shmoergh/hog-moduleur/05-adsr-vca/electronics/core/adsr-vca-core.kicad_pcb

## KiCad design 05-adsr-vca/electronics/core/adsr-vca-core.kicad_pcb (2025-10-25)

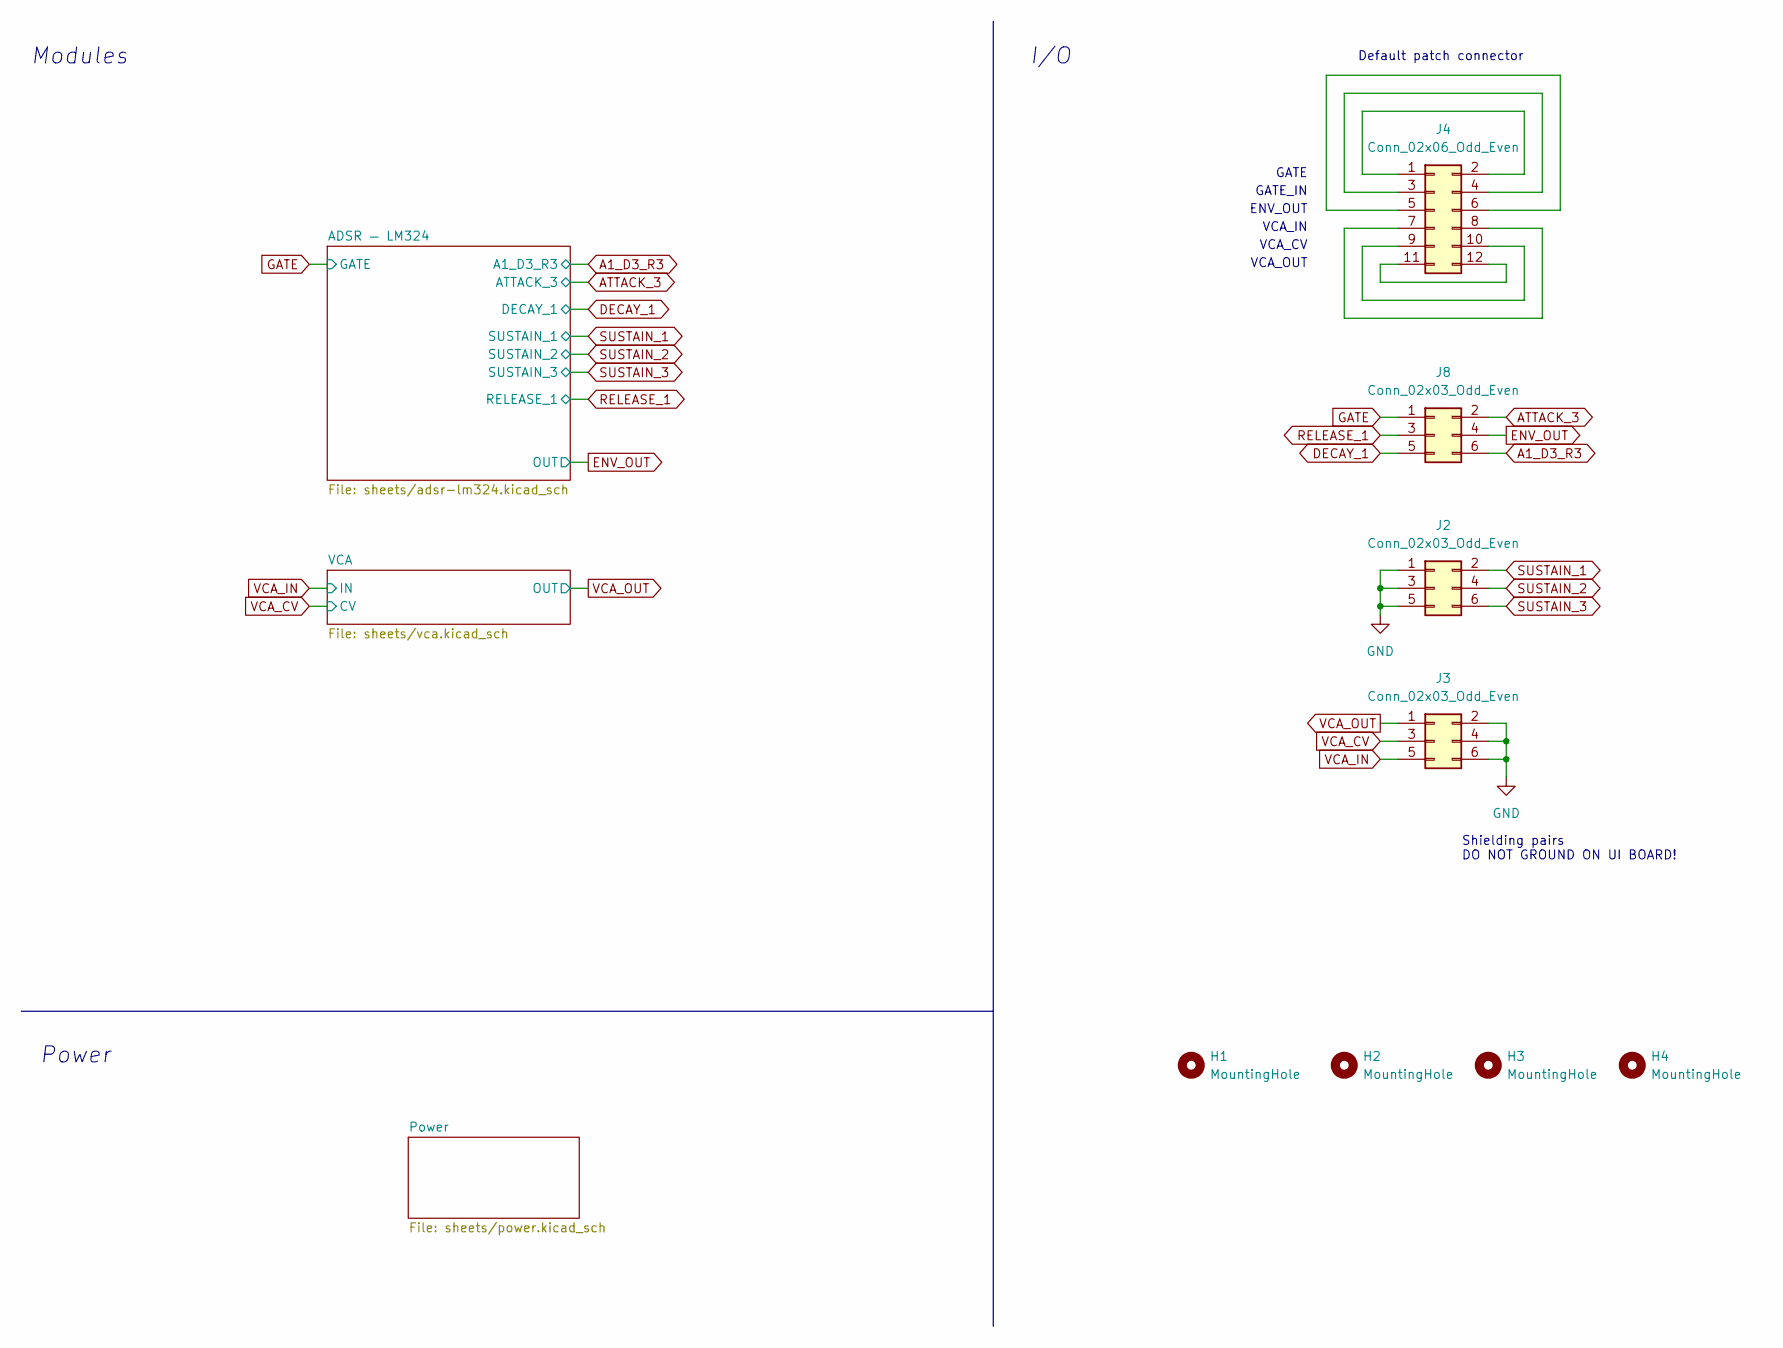
[picture p48: schematic adsr-vca-core.kicad_sch]

Parts:
H1, H2, H3, H4: MountingHole; MountingHole_3.2mm_M3_DIN965_Pad
J2, J3, J8: Conn_02x03_Odd_Even; PinHeader_2x03_P2.54mm_Vertical
J4: Conn_02x06_Odd_Even; PinHeader_2x06_P2.54mm_Vertical

Connections:
A1_D3_R3: J8.6; also elsewhere on the board
ATTACK_3: J8.2; also elsewhere on the board
DECAY_1: J8.5; also elsewhere on the board
ENV_OUT: J8.4; also elsewhere on the board
GATE: J8.1; also elsewhere on the board
GND: J2.1, J2.3, J2.5, J3.2, J3.4, J3.6; also elsewhere on the board
unnamed: J4.1, J4.2
unnamed: J4.3, J4.4
unnamed: J4.5, J4.6
unnamed: J4.7, J4.8
unnamed: J4.9, J4.10
unnamed: J4.11, J4.12
RELEASE_1: J8.3; also elsewhere on the board
SUSTAIN_1: J2.2; also elsewhere on the board
SUSTAIN_2: J2.4; also elsewhere on the board
SUSTAIN_3: J2.6; also elsewhere on the board
VCA_CV: J3.3; also elsewhere on the board
VCA_IN: J3.5; also elsewhere on the board
VCA_OUT: J3.1; also elsewhere on the board

Notes on the sheet:
Power
ENV_OUT
Default patch connector
VCA_OUT
GATE
Shielding pairs DO NOT GROUND ON UI BOARD!
VCA_CV
Modules
GATE_IN
I/O
VCA_IN

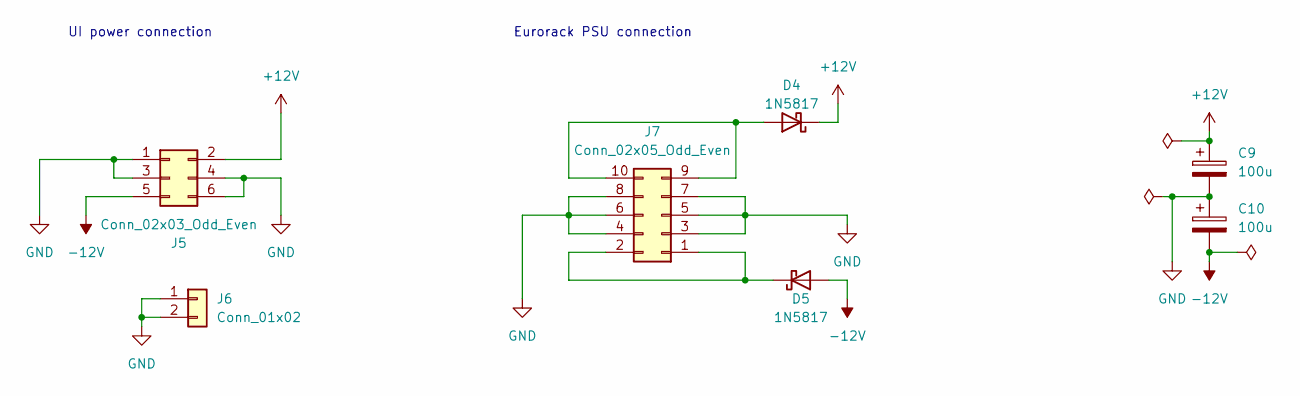
[picture p49: schematic power.kicad_sch]

Parts:
C9, C10: 100u; CP_Elec_6.3x7.7; LCSC C2836437
D4, D5: 1N5817; D_SOD-323; LCSC C5190152
J5: Conn_02x03_Odd_Even; PinHeader_2x03_P2.54mm_Vertical
J6: Conn_01x02; PinHeader_1x02_P2.54mm_Vertical
J7: Conn_02x05_Odd_Even; IDC-Header_2x05_P2.54mm_Horizontal

Connections:
+12V: C9.1, D4.1 (K), J5.2; also elsewhere on the board
-12V: C10.2, D5.2 (A), J5.5; also elsewhere on the board
GND: C9.2, C10.1, J5.1, J5.3, J5.4, J5.6, J6.1, J6.2, J7.3, J7.4, J7.5, J7.6, J7.7, J7.8; also elsewhere on the board
unnamed: D4.2 (A), J7.9, J7.10
unnamed: D5.1 (K), J7.1, J7.2

Notes on the sheet:
UI power connection
Eurorack PSU connection

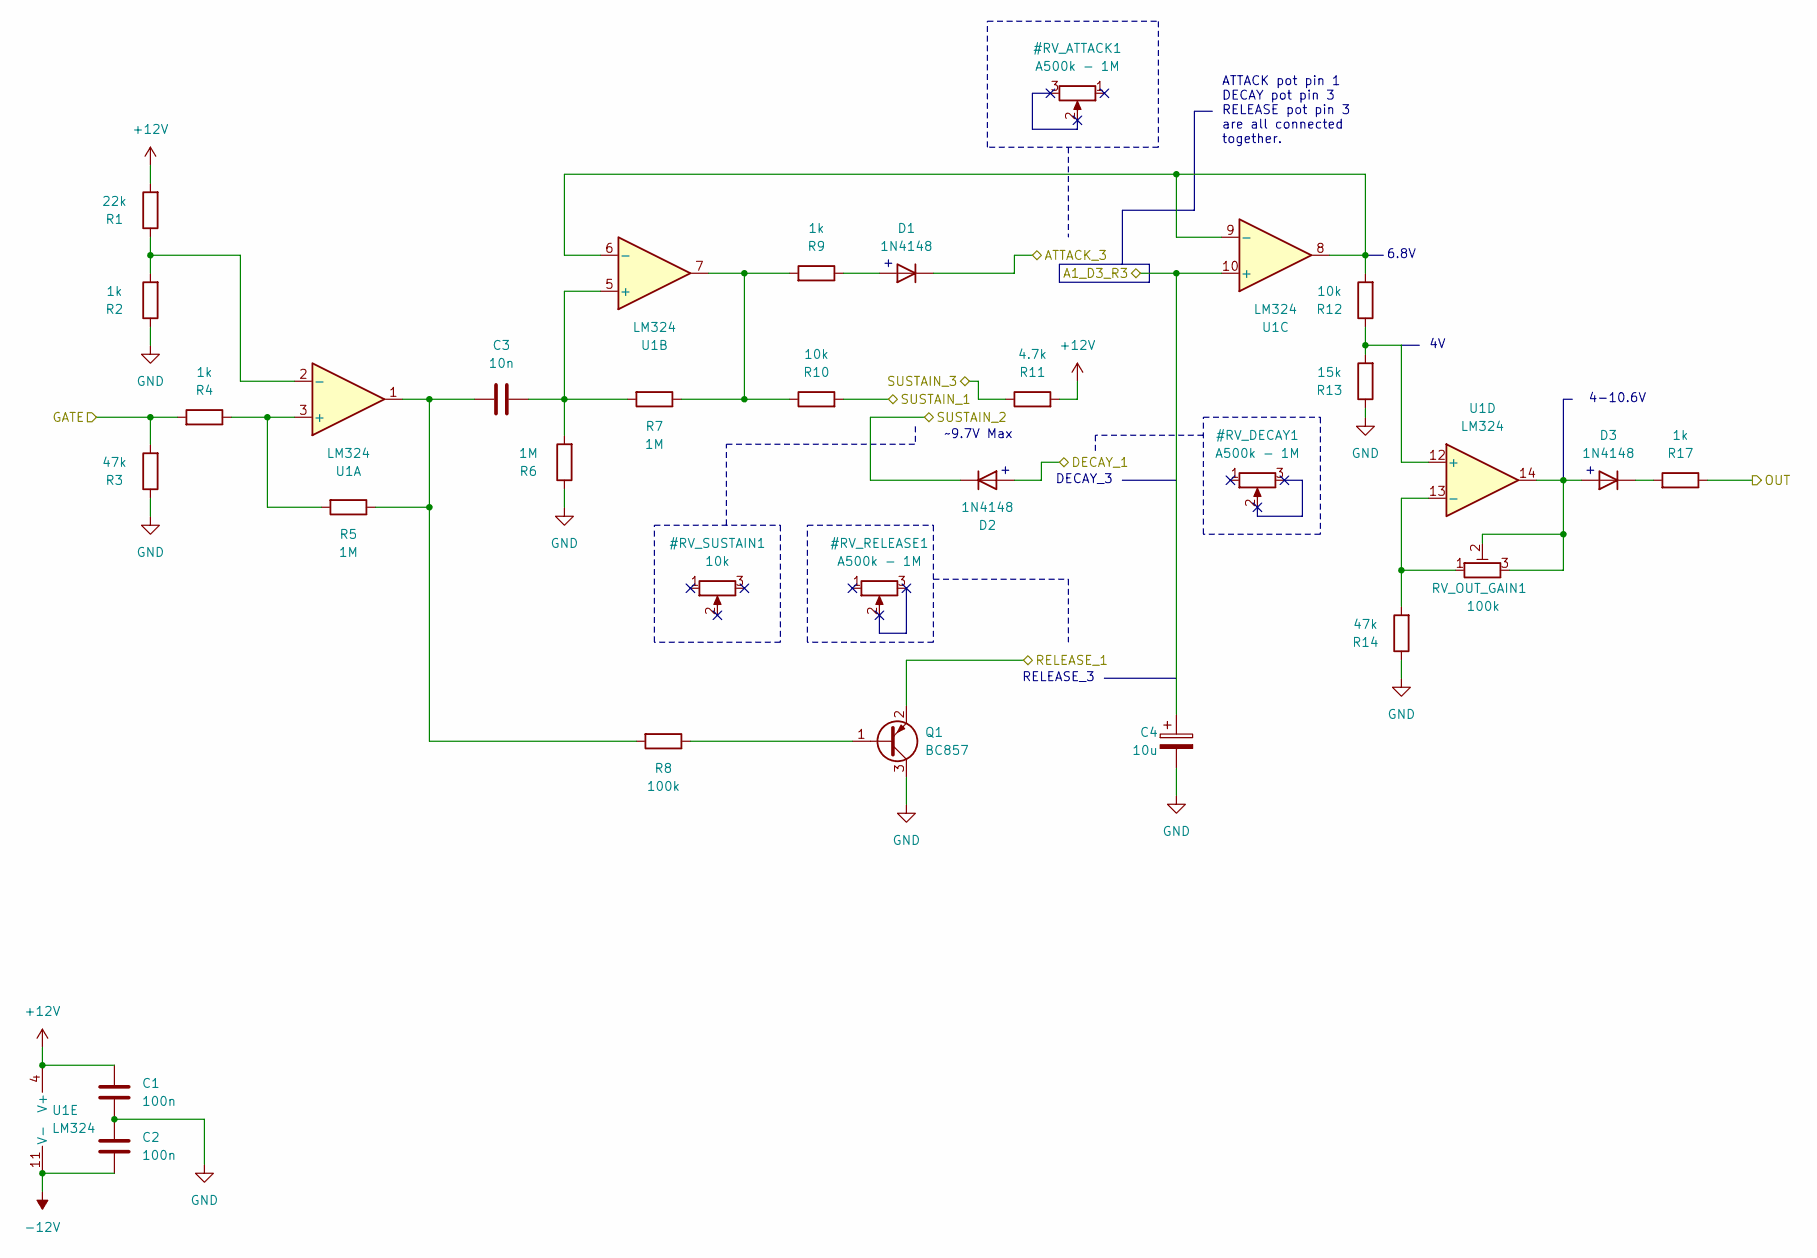
[picture p50: schematic adsr-lm324.kicad_sch, Hog Moduelur — ADSR]

Parts:
C1, C2: 100n; C_0603_1608Metric; LCSC C14663
C3: 10n; C_0603_1608Metric; LCSC C57112
C4: 10u; CP_Elec_5x5.4; LCSC C30110
D1, D2, D3: 1N4148; D_SOD-123; LCSC C81598
Q1: BC857; SOT-23; LCSC C20069137
R1: 22k; R_0603_1608Metric; LCSC C31850
R2, R4, R9, R17: 1k; R_0603_1608Metric; LCSC C21190
R3, R14: 47k; R_0603_1608Metric; LCSC C25819
R5, R6, R7: 1M; R_0603_1608Metric; LCSC C22935
R8: 100k; R_0603_1608Metric; LCSC C25803
R10, R12: 10k; R_0603_1608Metric; LCSC C25804
R11: 4.7k; R_0603_1608Metric; LCSC C23162
R13: 15k; R_0603_1608Metric; LCSC C22809
RV_OUT_GAIN1: 100k; Potentiometer_ACP_CA6-H2,5_Horizontal
U1: LM324; SOIC-14_3.9x8.7mm_P1.27mm; LCSC C71035

Connections:
+12V: C1.1, R1.2, R11.2, U1.4 (V+); also elsewhere on the board
-12V: C2.2, U1.11 (V-); also elsewhere on the board
A1_D3_R3: C4.1, U1.10 (+); also elsewhere on the board
ATTACK_3: D1.1 (K); also elsewhere on the board
DECAY_1: D2.2 (A); also elsewhere on the board
ENV_OUT: R17.1; also elsewhere on the board
GATE: R3.2, R4.2; also elsewhere on the board
GND: C1.2, C2.1, C4.2, Q1.3 (C), R2.1, R3.1, R6.1, R13.1, R14.1; also elsewhere on the board
unnamed: C3.1, R5.1, R8.2, U1.1
unnamed: D1.2 (A), R9.1
unnamed: D3.2 (A), RV_OUT_GAIN1.2, RV_OUT_GAIN1.3, U1.14
unnamed: D3.1 (K), R17.2
unnamed: Q1.1 (B), R8.1
unnamed: R7.1, R9.2, R10.1, U1.7
unnamed: R4.1, R5.2, U1.3 (+)
unnamed: R1.1, R2.2, U1.2 (-)
unnamed: C3.2, R6.2, R7.2, U1.5 (+)
unnamed: R12.2, U1.6 (-), U1.8, U1.9 (-)
unnamed: R12.1, R13.2, U1.12 (+)
unnamed: R14.2, RV_OUT_GAIN1.1, U1.13 (-)
RELEASE_1: Q1.2 (E); also elsewhere on the board
SUSTAIN_1: R10.2; also elsewhere on the board
SUSTAIN_2: D2.1 (K); also elsewhere on the board
SUSTAIN_3: R11.1; also elsewhere on the board

Notes on the sheet:
4-10.6V
DECAY_3
~9.7V Max
RELEASE_3
6.8V
ATTACK pot pin 1 DECAY pot pin 3 RELEASE pot pin 3 are all connected together.

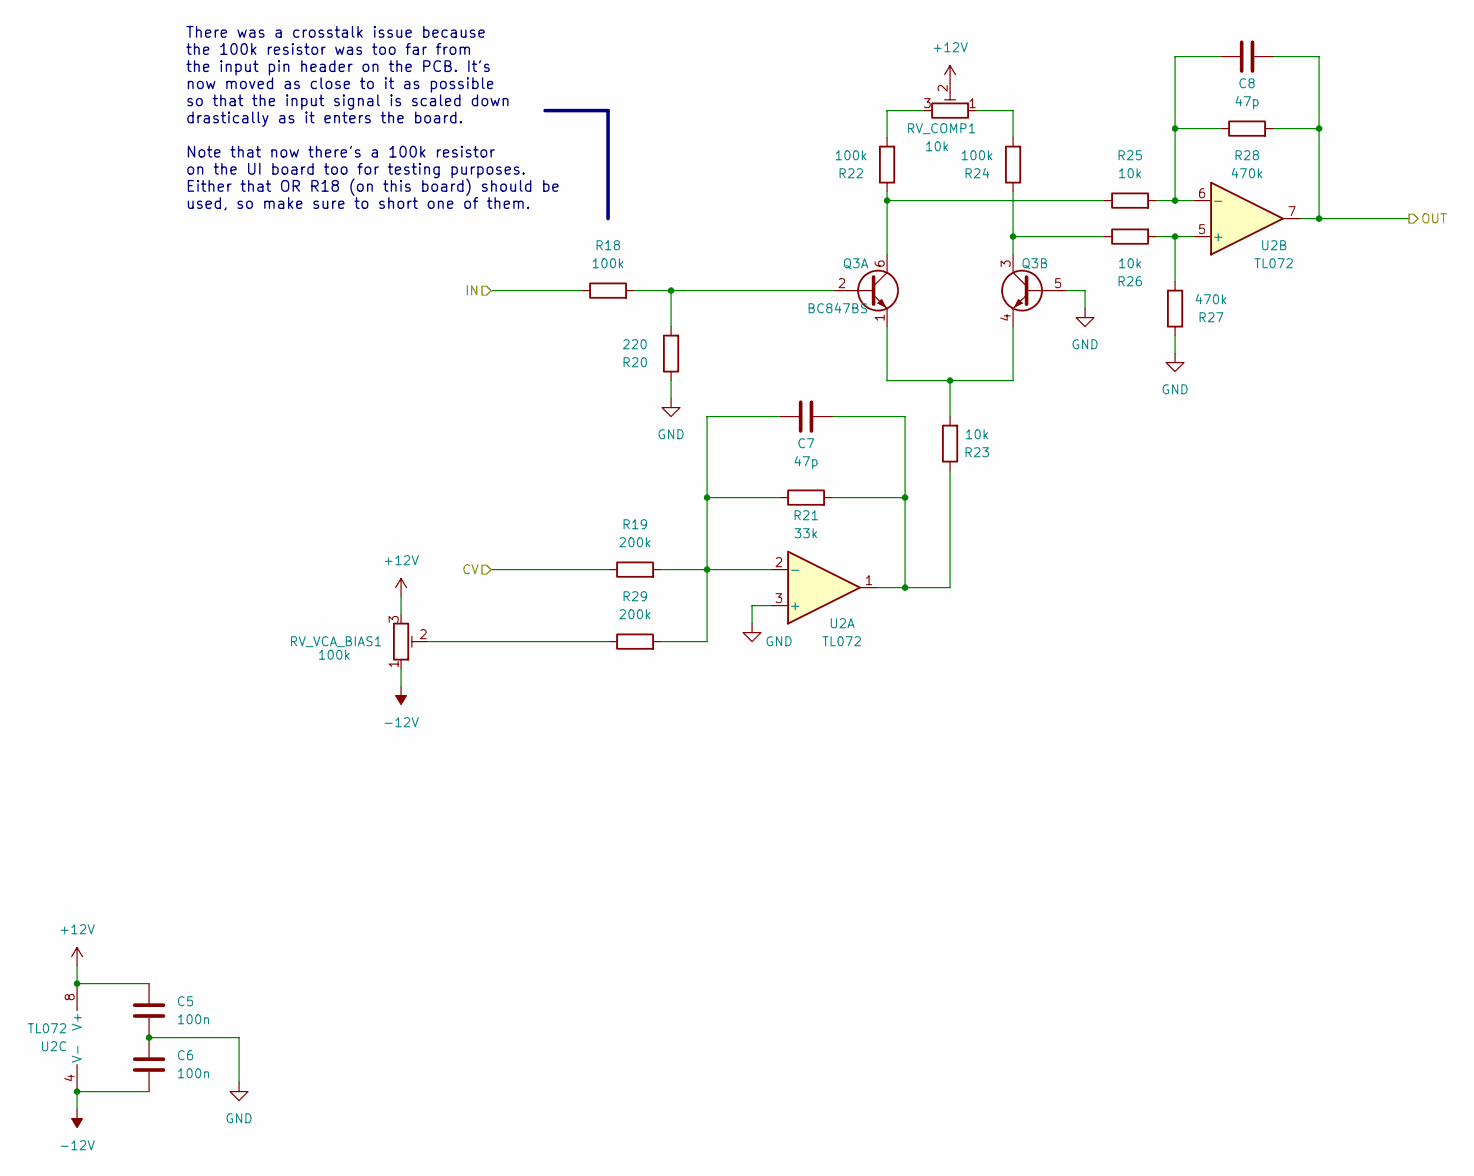
[picture p51: schematic vca.kicad_sch]

Parts:
C5, C6: 100n; C_0603_1608Metric; LCSC C14663
C7, C8: 47p; C_0603_1608Metric_Pad1.08x0.95mm_HandSolder; LCSC C1671
Q3: BC847BS; SOT-363_SC-70-6; LCSC C5380687
R18, R22, R24: 100k; R_0603_1608Metric; LCSC C25803
R19, R29: 200k; R_0603_1608Metric; LCSC C25811
R20: 220; R_0603_1608Metric; LCSC C22962
R21: 33k; R_0603_1608Metric; LCSC C4216
R23, R25, R26: 10k; R_0603_1608Metric; LCSC C25804
R27, R28: 470k; R_0603_1608Metric; LCSC C23178
RV_COMP1: 10k; Potentiometer_ACP_CA6-H2,5_Horizontal
RV_VCA_BIAS1: 100k; Potentiometer_ACP_CA6-H2,5_Horizontal
U2: TL072; SOIC-8_3.9x4.9mm_P1.27mm; LCSC C6961

Connections:
+12V: C5.1, RV_COMP1.2, RV_VCA_BIAS1.3, U2.8 (V+); also elsewhere on the board
-12V: C6.2, RV_VCA_BIAS1.1, U2.4 (V-); also elsewhere on the board
GND: C5.2, C6.1, Q3.5 (B2), R20.1, R27.1, U2.3 (+); also elsewhere on the board
unnamed: C7.2, R21.2, R23.1, U2.1
unnamed: Q3.2 (B1), R18.2, R20.2
unnamed: Q3.6 (C1), R22.1, R25.1
unnamed: Q3.1 (E1), Q3.4 (E2), R23.2
unnamed: Q3.3 (C2), R24.1, R26.1
unnamed: R22.2, RV_COMP1.3
unnamed: R24.2, RV_COMP1.1
unnamed: R29.1, RV_VCA_BIAS1.2
unnamed: C7.1, R19.2, R21.1, R29.2, U2.2 (-)
unnamed: R26.2, R27.2, U2.5 (+)
unnamed: C8.1, R25.2, R28.1, U2.6 (-)
VCA_CV: R19.1; also elsewhere on the board
VCA_IN: R18.1; also elsewhere on the board
VCA_OUT: C8.2, R28.2, U2.7; also elsewhere on the board

Notes on the sheet:
There was a crosstalk issue because the 100k resistor was too far from the input pin header on the PCB. It's now moved as close to it as possible so that the input signal is scaled down drastically as it enters the board. Note that now there's a 100k resistor on the UI board too for testing purpose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

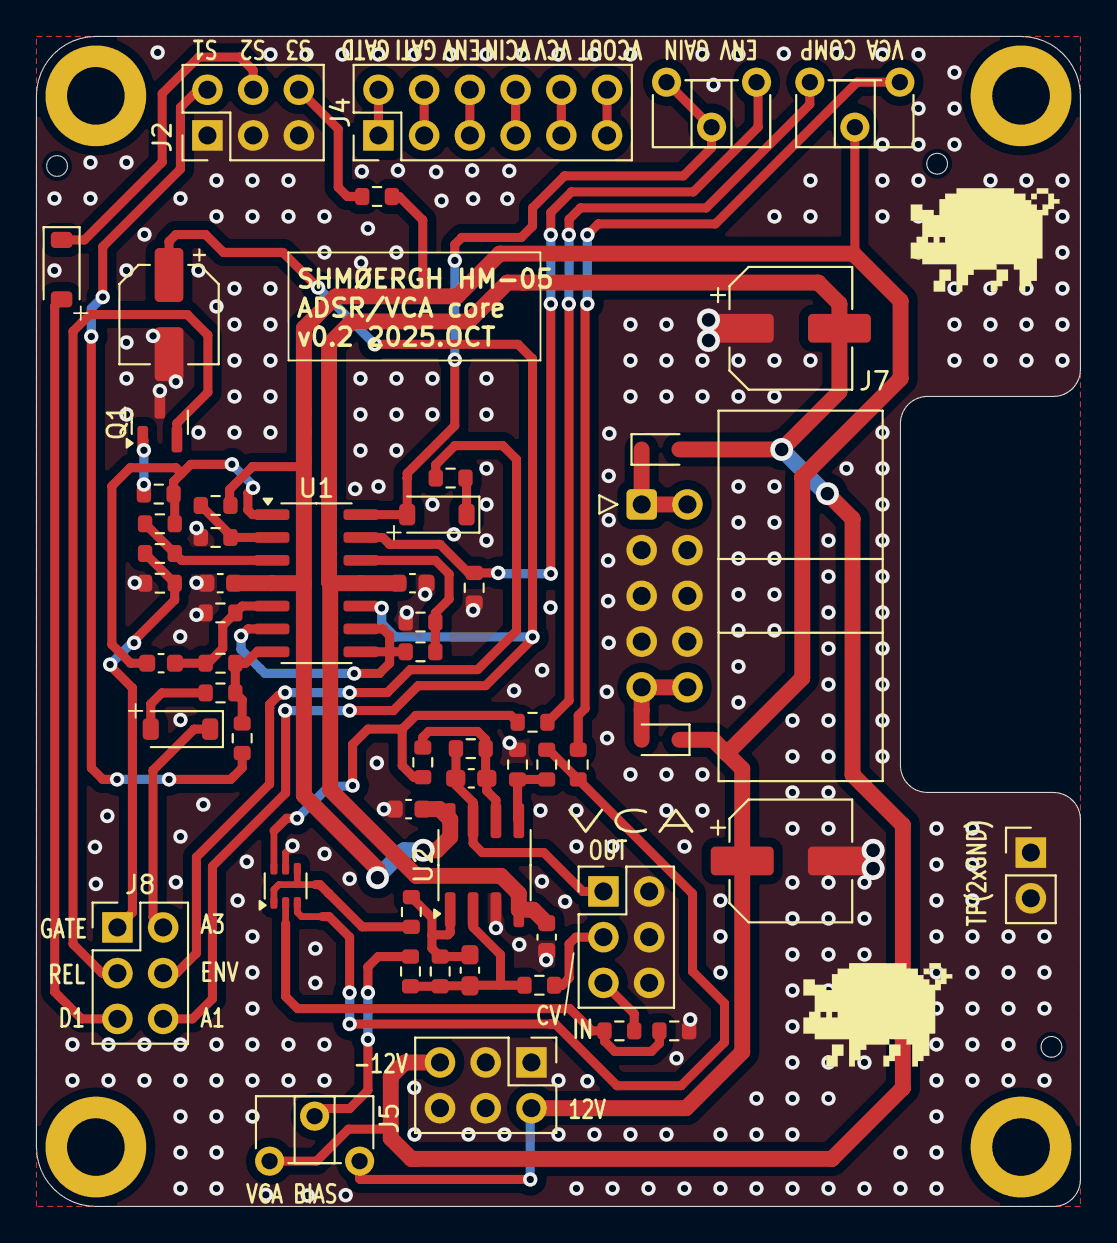
[picture p52: board adsr-vca-core.kicad_pcb from above]

Board: 2 copper layers, 58.0 x 65.0 mm, 60 parts (0 on the bottom side), 46 nets.
