shmoergh/hog-moduleur/04-vcf/electronics/core/vcf-core.kicad_pcb

## KiCad design 04-vcf/electronics/core/vcf-core.kicad_pcb (2025-10-25)

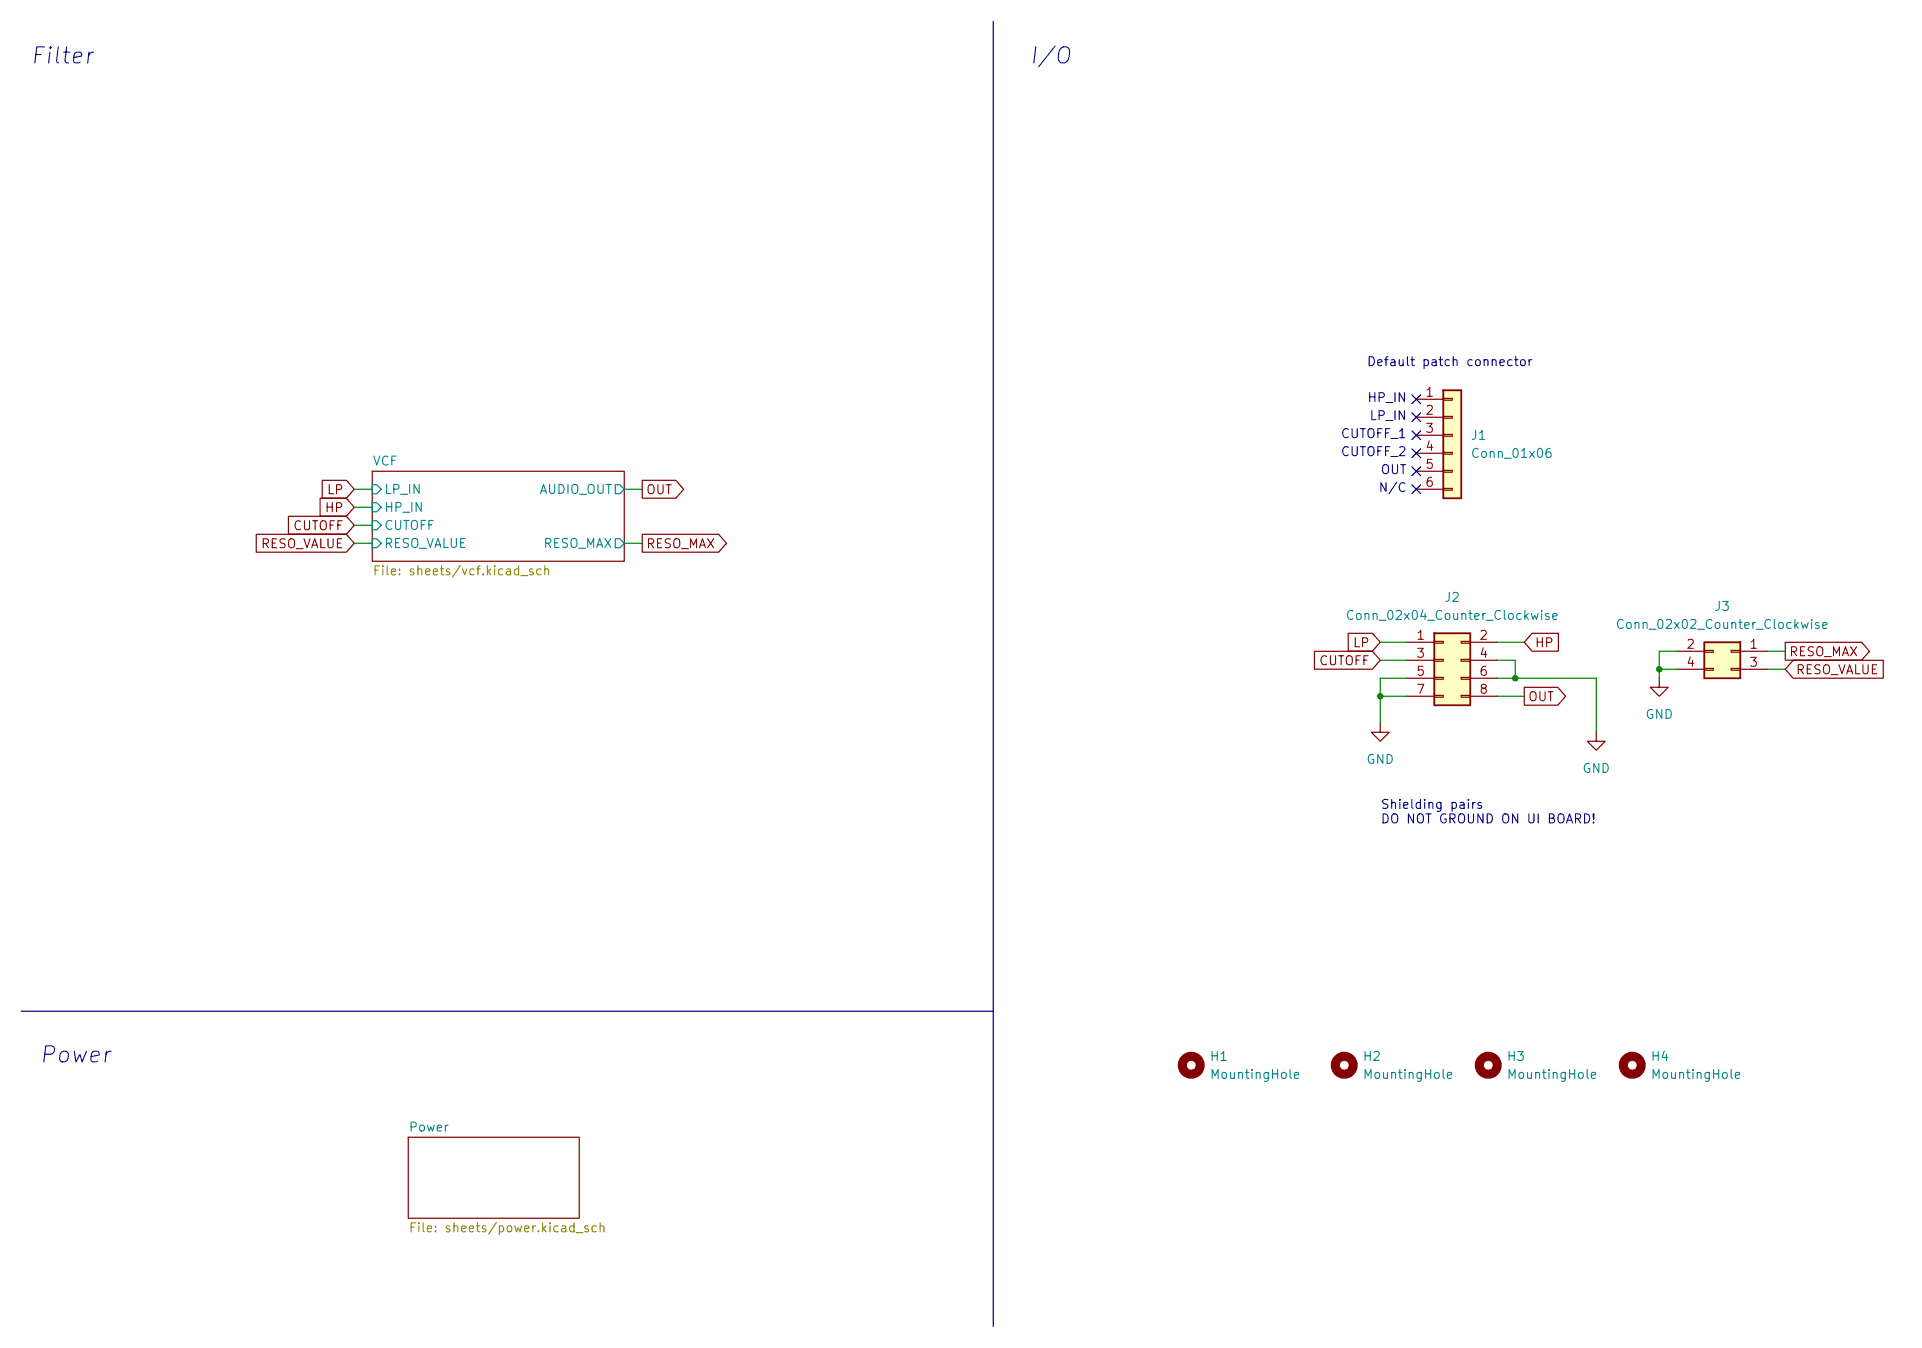
[picture p53: schematic vcf-core.kicad_sch, Hog Moduleur VCF]

Parts:
H1, H2, H3, H4: MountingHole; MountingHole_3.2mm_M3_DIN965_Pad
J1: Conn_01x06; PinHeader_1x06_P2.54mm_Vertical; Part no. 474-PRT-09280
J2: Conn_02x04_Counter_Clockwise; PinHeader_2x04_P2.54mm_Vertical; Part no. 200-HTSW10407TD
J3: Conn_02x02_Counter_Clockwise; PinHeader_2x02_P2.54mm_Vertical; Part no. 200-HTSW10207TD

Connections:
HP: J2.2; also elsewhere on the board
LP: J2.1; also elsewhere on the board
OUT: J2.8; also elsewhere on the board

Notes on the sheet:
Power
CUTOFF_1
Default patch connector
N/C
HP_IN
Shielding pairs DO NOT GROUND ON UI BOARD!
OUT
Filter
LP_IN
I/O
CUTOFF_2
