shmoergh/hog-moduleur/04-vcf/electronics/core/vcf-core.kicad_pcb

## KiCad design 04-vcf/electronics/core/vcf-core.kicad_pcb (continued)

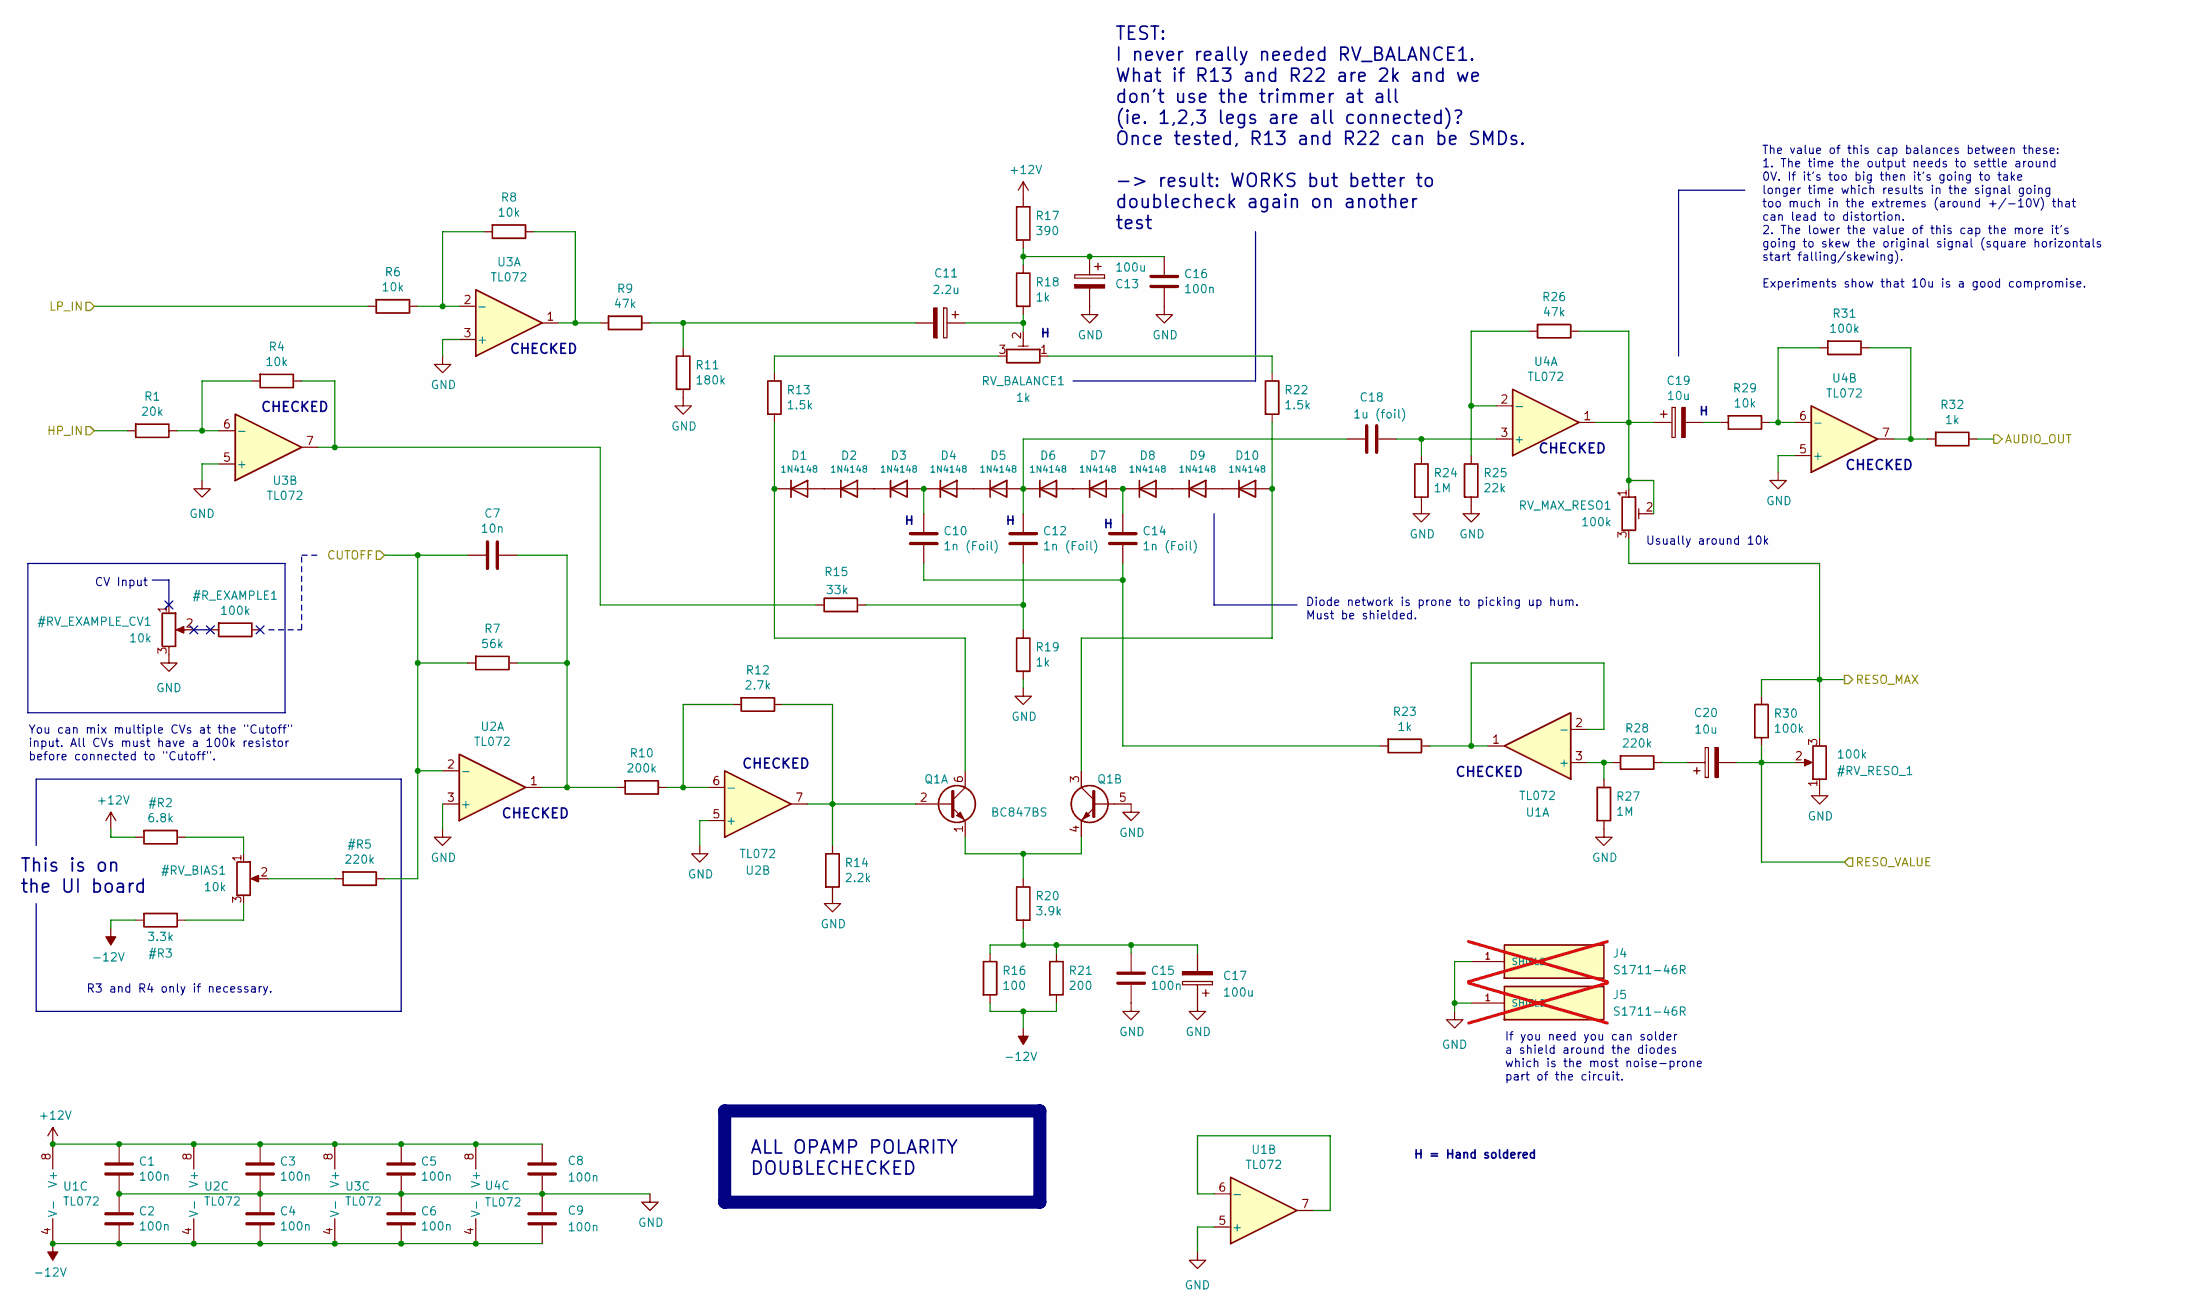
[picture p54: schematic vcf.kicad_sch]

Parts:
C1, C2, C3, C4, C5, C6, C8, C9, C15, C16: 100n; C_0603_1608Metric; LCSC C14663
C7: 10n; C_0603_1608Metric; LCSC C57112
C10, C12, C14: 1n (Foil); C_Rect_L7.0mm_W2.5mm_P5.00mm; Part no. 80-R82EC1100SH50J
C11: 2.2u; CP_Elec_4x5.7; LCSC C249889
C13, C17: 100u; CP_Elec_6.3x7.7; LCSC C2836437
C18: 1u (foil); C_Rect_L7.0mm_W4.5mm_P5.00mm; Part no. 80-R82EC1470DQ50K
C19: 10u; CP_Radial_D8.0mm_P5.00mm; Part no. 667-EEA-GA1V470B
C20: 10u; CP_Elec_4x5.4; LCSC C3343
D1, D2, D3, D4, D5, D6, D7, D8, D9, D10: 1N4148; D_SOD-123; LCSC C81598
J4, J5: S1711-46R; HARWIN_S1711-46R; PARTREV 23/10/18; not fitted
Q1: BC847BS; SOT-363_SC-70-6; LCSC C5380687
R1: 20k; R_0603_1608Metric_Pad0.98x0.95mm_HandSolder; LCSC C4184
R4, R6, R8, R29: 10k; R_0603_1608Metric_Pad0.98x0.95mm_HandSolder; LCSC C25804
R7: 56k; R_0603_1608Metric_Pad0.98x0.95mm_HandSolder; LCSC C23206
R9, R26: 47k; R_0603_1608Metric_Pad0.98x0.95mm_HandSolder; LCSC C25819
R10: 200k; R_0603_1608Metric_Pad0.98x0.95mm_HandSolder; LCSC C25811
R11: 180k; R_0603_1608Metric_Pad0.98x0.95mm_HandSolder; LCSC C3016400
R12: 2.7k; R_0603_1608Metric_Pad0.98x0.95mm_HandSolder; LCSC C13167
R13, R22: 1.5k; R_0603_1608Metric_Pad0.98x0.95mm_HandSolder
R14: 2.2k; R_0603_1608Metric_Pad0.98x0.95mm_HandSolder; LCSC C4190
R15: 33k; R_0603_1608Metric_Pad0.98x0.95mm_HandSolder; LCSC C4216
R16: 100; R_0603_1608Metric_Pad0.98x0.95mm_HandSolder; LCSC C22775
R17: 390; R_0603_1608Metric_Pad0.98x0.95mm_HandSolder; LCSC C23151
R18, R19, R23, R32: 1k; R_0603_1608Metric_Pad0.98x0.95mm_HandSolder; LCSC C21190
R20: 3.9k; R_0603_1608Metric_Pad0.98x0.95mm_HandSolder; LCSC C23018
R21: 200; R_0603_1608Metric_Pad0.98x0.95mm_HandSolder; LCSC C8218
R24, R27: 1M; R_0603_1608Metric_Pad0.98x0.95mm_HandSolder; LCSC C22935
R25: 22k; R_0603_1608Metric_Pad0.98x0.95mm_HandSolder; LCSC C31850
R28: 220k; R_0603_1608Metric_Pad0.98x0.95mm_HandSolder; LCSC C22961
R30, R31: 100k; R_0603_1608Metric_Pad0.98x0.95mm_HandSolder; LCSC C25803
RV_BALANCE1: 1k; Potentiometer_ACP_CA6-H2,5_Horizontal; Part no. 531-PT6KH-1K
RV_MAX_RESO1: 100k; Potentiometer_ACP_CA6-H2,5_Horizontal; Part no. 531-PT6KH104A1010PM
U1, U2, U3, U4: TL072; SOIC-8_3.9x4.9mm_P1.27mm; LCSC C6961

Connections:
HP: R1.2; also elsewhere on the board
LP: R6.2; also elsewhere on the board
unnamed: C7.1, R7.1, R10.2, U2.1
unnamed: C10.2, C14.2, R23.2
unnamed: C11.1, R18.2, RV_BALANCE1.2
unnamed: C11.2, R9.1, R11.1
unnamed: C12.2, R15.2, R19.1
unnamed: C13.1, C16.1, R17.2, R18.1
unnamed: C15.1, C17.2, R16.1, R20.2, R21.1
unnamed: C19.1, R26.1, RV_MAX_RESO1.1, RV_MAX_RESO1.2, U4.1
unnamed: C19.2, R29.2
unnamed: C20.1, R28.1
unnamed: D1.2 (A), D2.1 (K)
unnamed: D1.1 (K), Q1.6 (C1), R13.2
unnamed: D2.2 (A), D3.1 (K)
unnamed: C10.1, D3.2 (A), D4.1 (K)
unnamed: D4.2 (A), D5.1 (K)
unnamed: C12.1, C18.2, D5.2 (A), D6.1 (K)
unnamed: D6.2 (A), D7.1 (K)
unnamed: C14.1, D7.2 (A), D8.1 (K)
unnamed: D8.2 (A), D9.1 (K)
unnamed: D10.2 (A), Q1.3 (C2), R22.2
unnamed: D9.2 (A), D10.1 (K)
unnamed: Q1.2 (B1), R12.1, R14.1, U2.7
unnamed: Q1.1 (E1), Q1.4 (E2), R20.1
unnamed: R8.1, R9.2, U3.1
unnamed: R13.1, RV_BALANCE1.3
unnamed: R4.1, R15.1, U3.7
unnamed: R22.1, RV_BALANCE1.1
unnamed: R31.1, R32.2, U4.7
unnamed: R27.1, R28.2, U1.3 (+)
unnamed: R23.1, U1.1, U1.2 (-)
unnamed: U1.6 (-), U1.7
unnamed: R10.1, R12.2, U2.6 (-)
unnamed: R6.1, R8.2, U3.2 (-)
unnamed: R1.1, R4.2, U3.6 (-)
unnamed: C18.1, R24.1, U4.3 (+)
unnamed: R25.1, R26.2, U4.2 (-)
unnamed: R29.1, R31.2, U4.6 (-)
OUT: R32.1; also elsewhere on the board

Notes on the sheet:
R3 and R4 only if necessary.
CHECKED
CV Input
If you need you can solder a shield around the diodes which is the most noise-prone part of the circuit.
ALL OPAMP POLARITY DOUBLECHECKED
This is on the UI board
Diode network is prone to picking up hum. Must be shielded.
You can mix multiple CVs at the "Cutoff" input. All CVs must have a 100k resistor before connected to "Cutoff".
The value of this cap balances between these: 1. The time the output needs to settle around 0V. If it's too big then it's going to take longer time which results in the signal going too much in the extremes (around +/-10V) that can lead to distortion. 2. The lower the value of this cap the more it'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
Usually around 10k
H = Hand soldered
TEST: I never really needed RV_BALANCE1. What if R13 and R22 are 2k and we don't use the trimmer at all (ie. 1,2,3 legs are all connected)? Once tested, R13 and R22 can be SMDs. -> result: WORKS but better to doublecheck again on another test

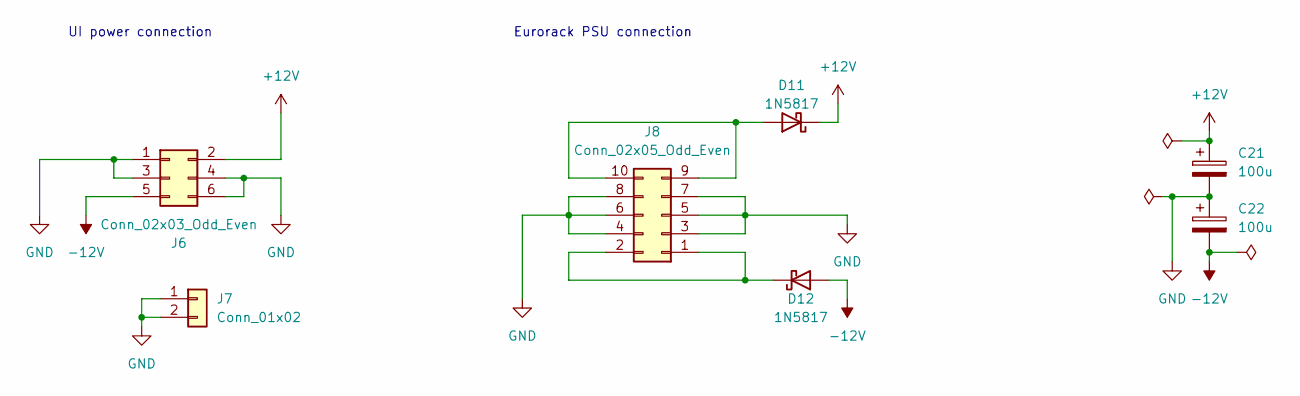
[picture p55: schematic power.kicad_sch]

Parts:
C21, C22: 100u; CP_Elec_6.3x7.7; LCSC C2836437
D11, D12: 1N5817; D_SOD-323; LCSC C5190152
J6: Conn_02x03_Odd_Even; PinHeader_2x03_P2.54mm_Vertical; Part no. 200-TSW10307TD
J7: Conn_01x02; PinHeader_1x02_P2.54mm_Vertical; Part no. 200-HTSW10207TS
J8: Conn_02x05_Odd_Even; IDC-Header_2x05_P2.54mm_Horizontal; Part no. 571-5103310-1

Connections:
unnamed: D11.2 (A), J8.9, J8.10
unnamed: D12.1 (K), J8.1, J8.2

Notes on the sheet:
UI power connection
Eurorack PSU connection

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
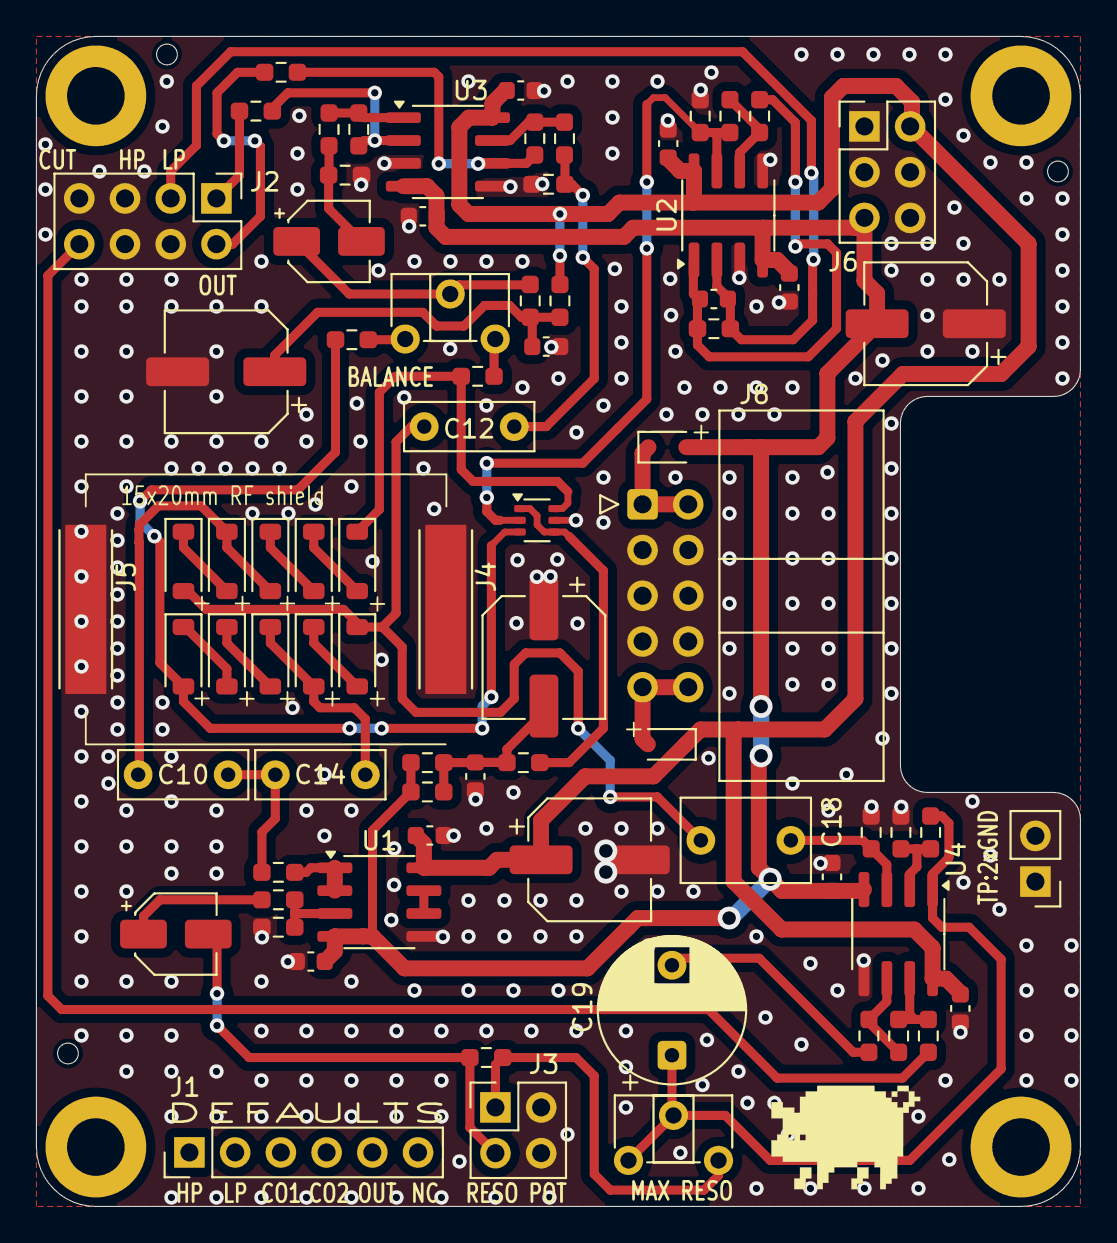
[picture p56: board vcf-core.kicad_pcb from above]

Board: 2 copper layers, 58.0 x 65.0 mm, 82 parts (0 on the bottom side), 48 nets.
