shmoergh/hog-moduleur/01-psu/electronics/v0.2/psu.kicad_pcb

## KiCad design 01-psu/electronics/v0.2/psu.kicad_pcb (2025-10-25)

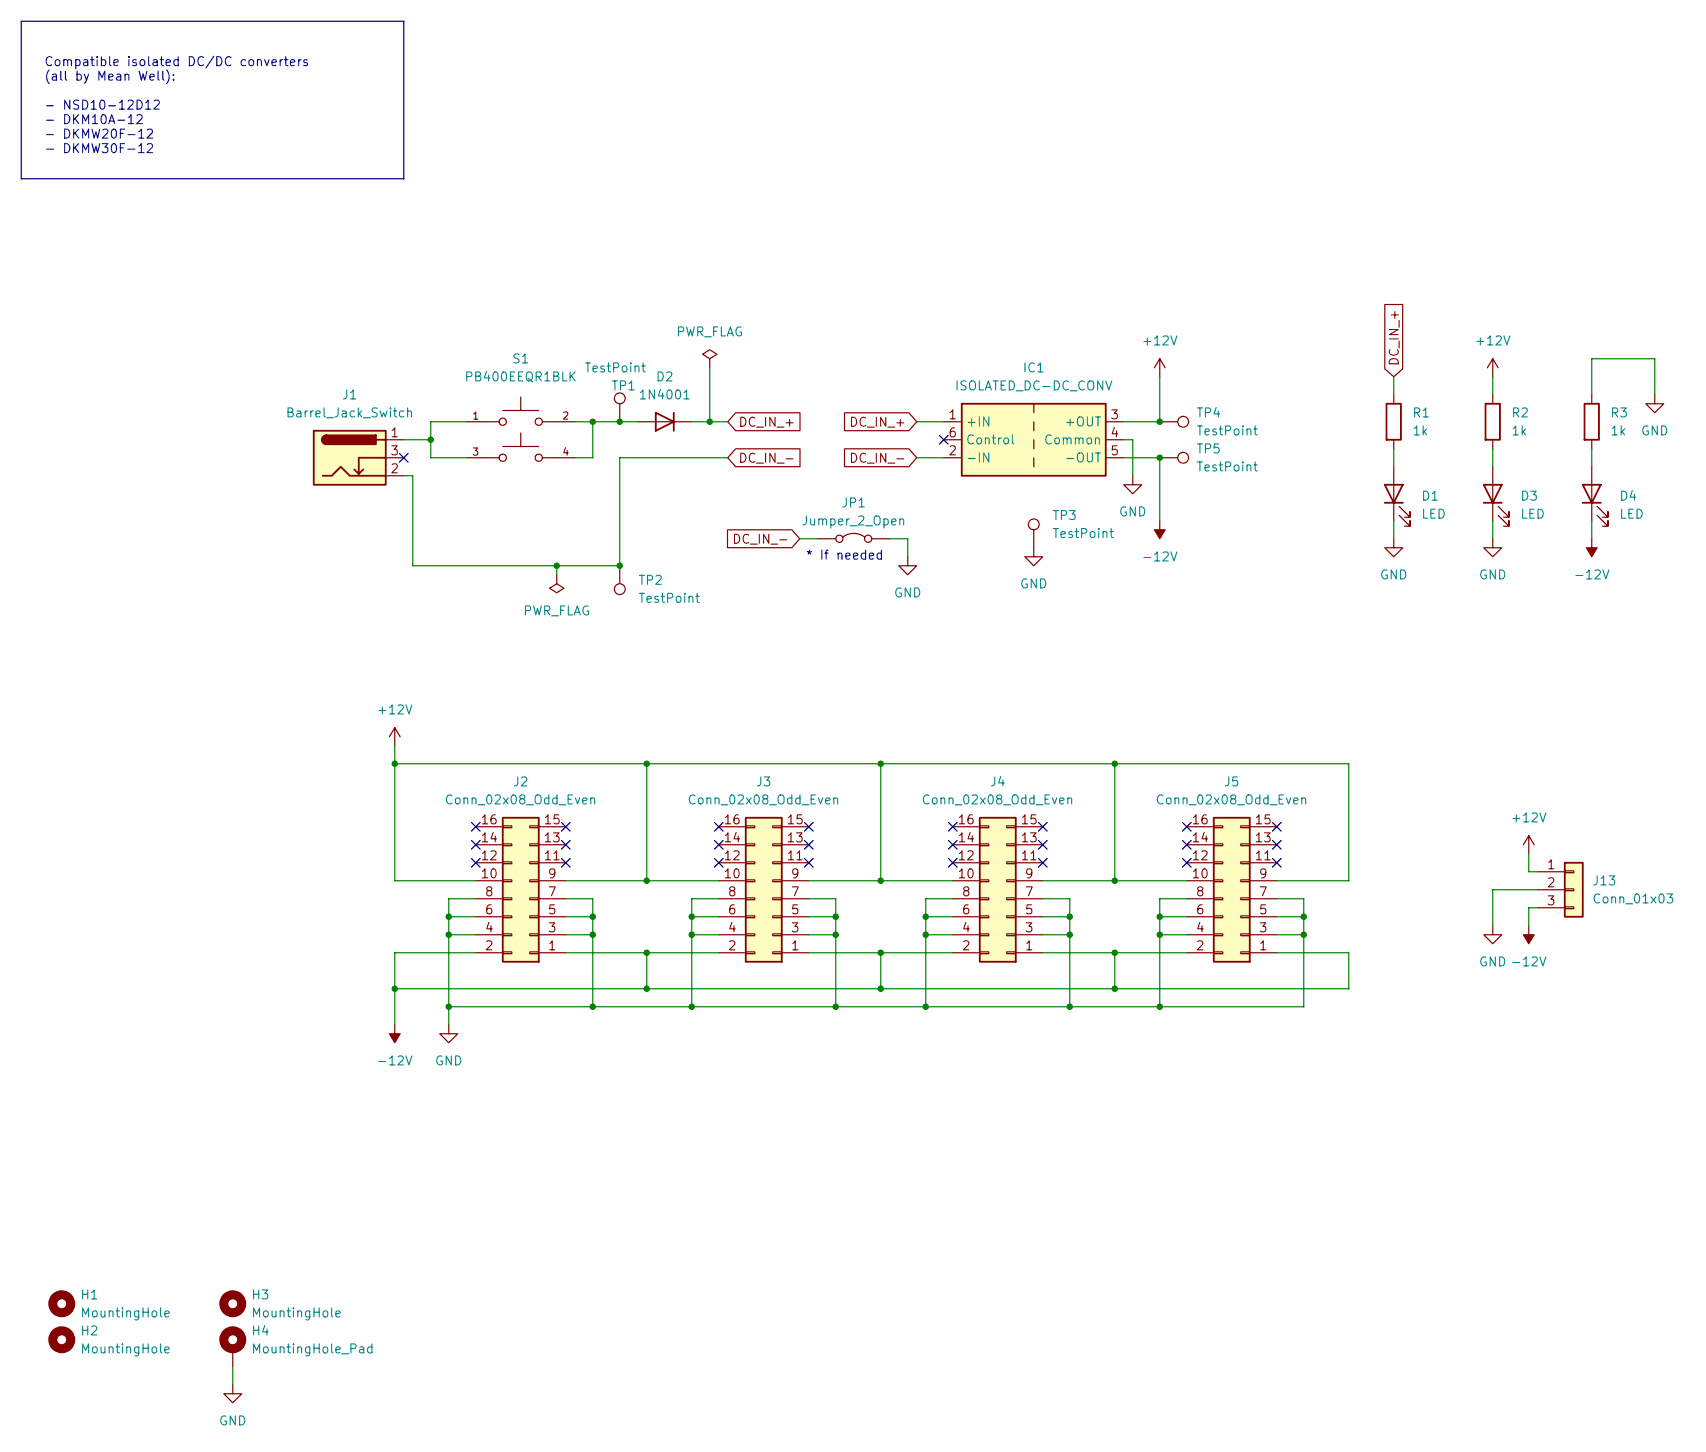
[picture p57: schematic psu.kicad_sch, Hog Moduleur PSU]

Parts:
D1, D3, D4: LED; LED_D3.0mm; Part No. 604-WP710A10ID
D2: 1N4001; D_DO-41_SOD81_P7.62mm_Horizontal; Part No. 637-1N4001
H1, H2, H3: MountingHole; MountingHole_3.2mm_M3_DIN965; Part No. N/A
H4: MountingHole_Pad; MountingHole_3.2mm_M3_DIN965_Pad
IC1: ISOLATED_DC-DC_CONV; Converter_DCDC_MeanWell_NSD10_DKMW_THT; Manufacturer_Part_Number NSD10-12D12; Mouser Part Number 709-NSD10-12D5
J1: Barrel_Jack_Switch; BarrelJack_Wuerth_6941xx301002; Part No. 710-694106301002
J2, J3, J4, J5: Conn_02x08_Odd_Even; IDC-Header_2x08_P2.54mm_Horizontal; Part No. 737-BHR-16-VUA
J13: Conn_01x03; PinHeader_1x03_P2.54mm_Vertical
JP1: Jumper_2_Open; SolderJumper-2_P1.3mm_Bridged2Bar_RoundedPad1.0x1.5mm; Part No. N/A
R1, R2, R3: 1k; R_Axial_DIN0207_L6.3mm_D2.5mm_P7.62mm_Horizontal; Part No. 303-MF0W4FF1001A10
S1: PB400EEQR1BLK; SW_PB400EEQR1BLK; PARTREV A
TP1, TP2, TP3, TP4, TP5: TestPoint; TestPoint_THTPad_2.0x2.0mm_Drill1.0mm; Part No. N/A

Connections:
+12V: IC1.3 (+OUT), J2.9, J2.10, J3.9, J3.10, J4.9, J4.10, J5.9, J5.10, J13.1, R2.1, TP4.1
-12V: D4.1 (K), IC1.5 (-OUT), J2.1, J2.2, J3.1, J3.2, J4.1, J4.2, J5.1, J5.2, J13.3, TP5.1
DC_IN_+: D2.1 (K), IC1.1 (+IN), R1.1
DC_IN_-: IC1.2 (-IN), J1.2, JP1.1 (A), TP2.1
GND: D1.1 (K), D3.1 (K), H4.1, IC1.4 (Common), J2.3, J2.4, J2.5, J2.6, J2.7, J2.8, J3.3, J3.4, J3.5, J3.6, J3.7, J3.8, J4.3, J4.4, J4.5, J4.6, J4.7, J4.8, J5.3, J5.4, J5.5, J5.6, J5.7, J5.8, J13.2, JP1.2 (B), R3.1, TP3.1
unnamed: D1.2 (A), R1.2
unnamed: D2.2 (A), S1.2, S1.4, TP1.1
unnamed: D3.2 (A), R2.2
unnamed: D4.2 (A), R3.2
unnamed: J1.1, S1.1, S1.3

Notes on the sheet:
Compatible isolated DC/DC converters (all by Mean Well): - NSD10-12D12 - DKM10A-12 - DKMW20F-12 - DKMW30F-12
* If needed

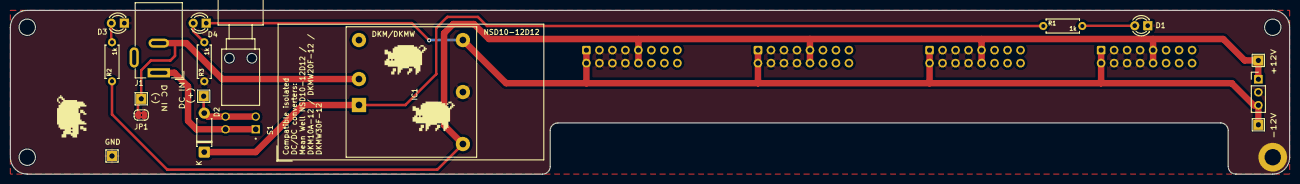
[picture p58: board psu.kicad_pcb from above]

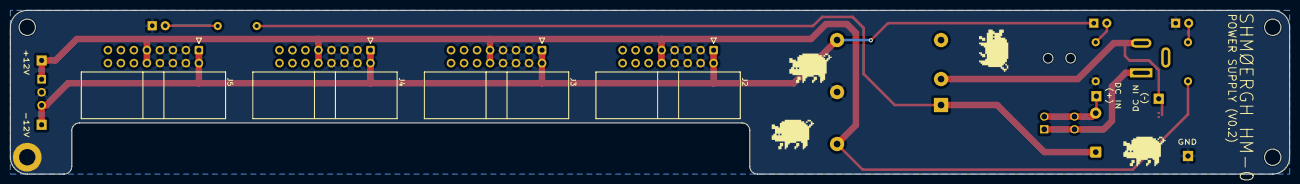
[picture p59: board psu.kicad_pcb from below]

Board: 2 copper layers, 250.0 x 32.0 mm, 25 parts (4 on the bottom side), 10 nets.
