shmoergh/hog-moduleur/02-vco/electronics/core/vco-core.kicad_pcb

## KiCad design 02-vco/electronics/core/vco-core.kicad_pcb (2025-10-25)

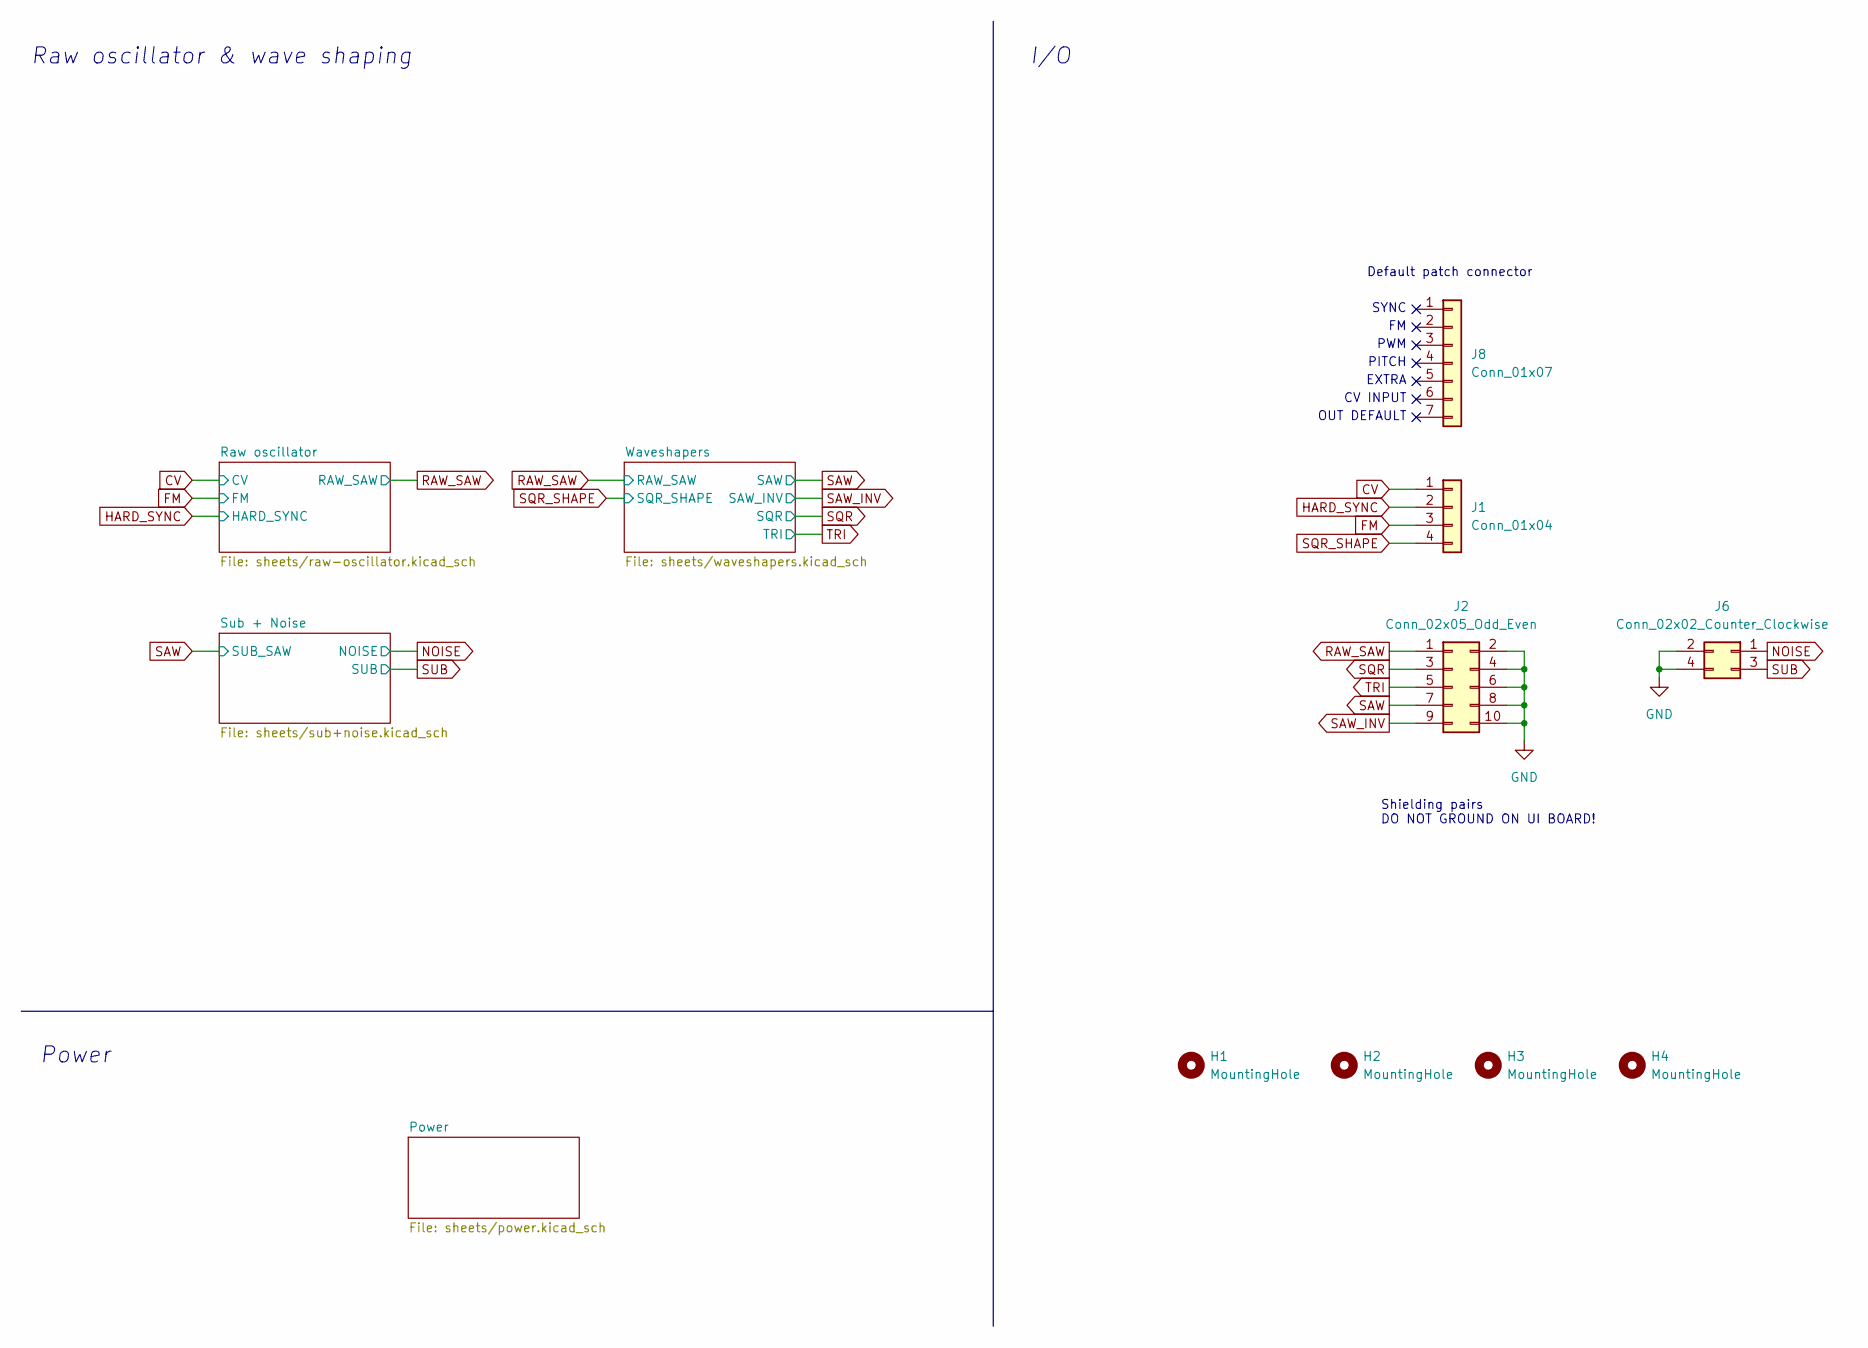
[picture p60: schematic vco-core.kicad_sch, Hog Moduleur VCO core]

Parts:
H1, H2, H3, H4: MountingHole; MountingHole_3.2mm_M3_DIN965_Pad
J1: Conn_01x04; PinHeader_1x04_P2.54mm_Vertical; Mouser Part no. 200-HTSW10407TS
J2: Conn_02x05_Odd_Even; PinHeader_2x05_P2.54mm_Vertical; Mouser Part no. 200-TSW10507TD
J6: Conn_02x02_Counter_Clockwise; PinHeader_2x02_P2.54mm_Vertical; Mouser Part no. 200-HTSW10207TD
J8: Conn_01x07; PinHeader_1x07_P2.54mm_Vertical; Mouser Part no. 474-PRT-09280

Connections:
CV: J1.1; also elsewhere on the board
FM: J1.3; also elsewhere on the board
GND: J2.2, J2.4, J2.6, J2.8, J2.10, J6.2, J6.4; also elsewhere on the board
HARD_SYNC: J1.2; also elsewhere on the board
NOISE: J6.1; also elsewhere on the board
RAW_SAW: J2.1; also elsewhere on the board
SAW: J2.7; also elsewhere on the board
SAW_INV: J2.9; also elsewhere on the board
SQR: J2.3; also elsewhere on the board
SUB: J6.3; also elsewhere on the board
TRI: J2.5; also elsewhere on the board

Notes on the sheet:
Power
PWM
Default patch connector
CV INPUT
SYNC
OUT DEFAULT
Shielding pairs DO NOT GROUND ON UI BOARD!
EXTRA
Raw oscillator & wave shaping
I/O
PITCH

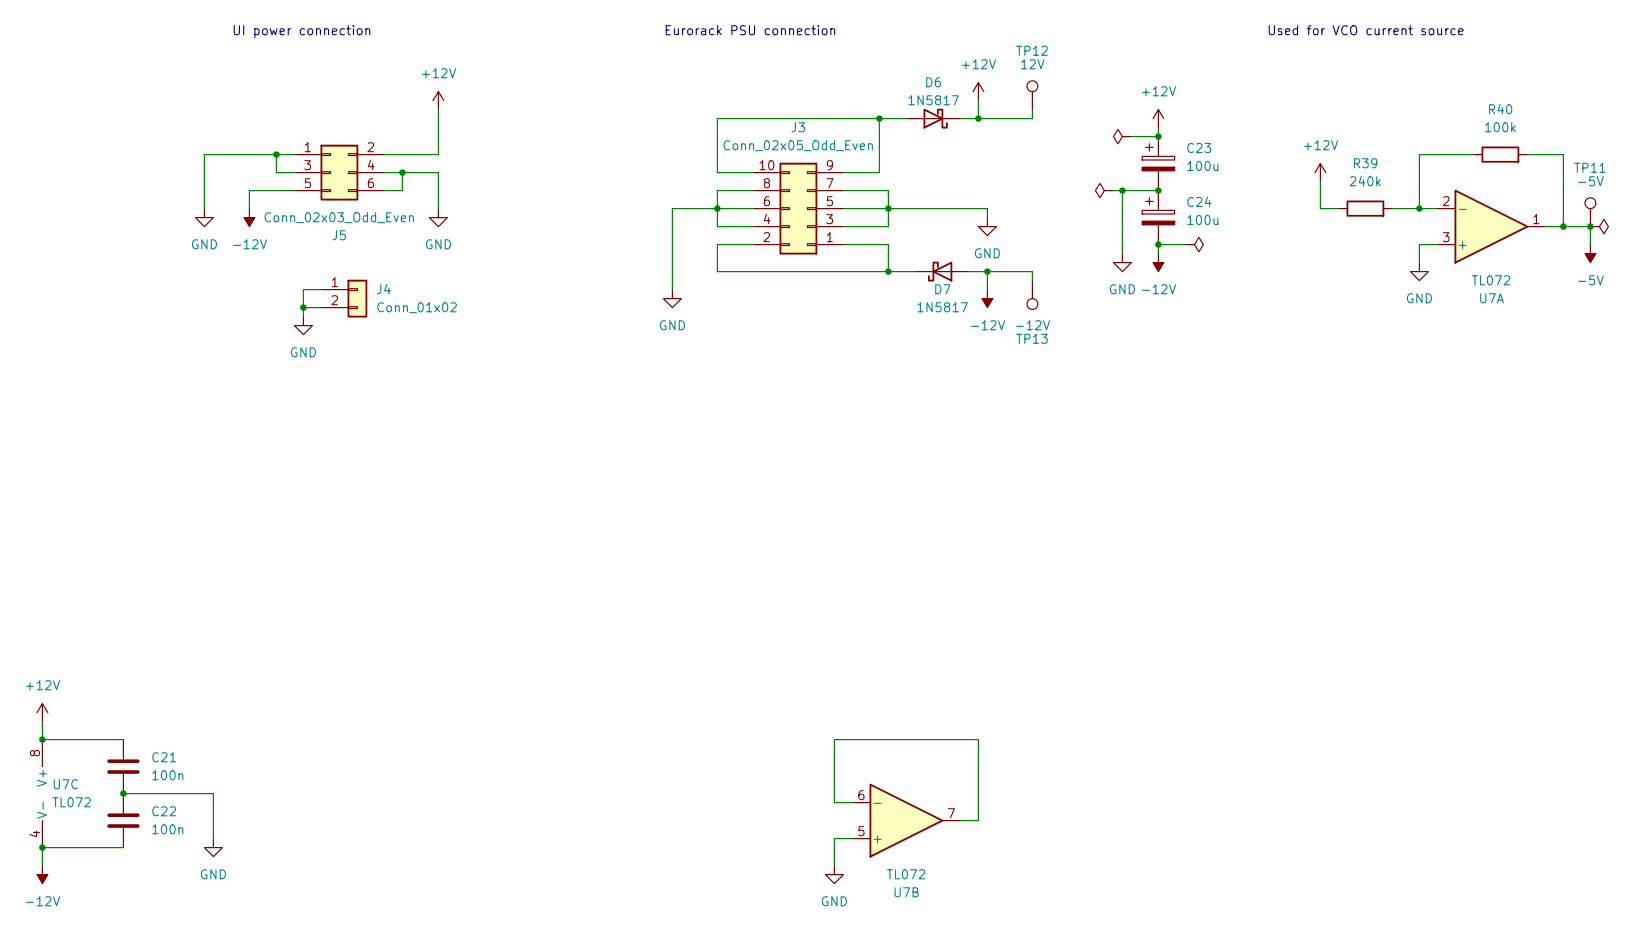
[picture p61: schematic power.kicad_sch]

Parts:
C21, C22: 100n; C_0603_1608Metric; LCSC C14663
C23, C24: 100u; CP_Elec_6.3x7.7; LCSC C2836437
D6, D7: 1N5817; D_SOD-323; LCSC C5190152
J3: Conn_02x05_Odd_Even; IDC-Header_2x05_P2.54mm_Horizontal; Mouser Part no. 571-5103310-1
J4: Conn_01x02; PinHeader_1x02_P2.54mm_Vertical; Mouser Part no. 200-HTSW10207TS
J5: Conn_02x03_Odd_Even; PinHeader_2x03_P2.54mm_Vertical; Mouser Part no. 200-TSW10307TD
R39: 240k; R_0603_1608Metric; LCSC C4197
R40: 100k; R_0603_1608Metric; LCSC C25803
TP11: -5V; TestPoint_THTPad_2.0x2.0mm_Drill1.0mm
TP12: 12V; TestPoint_THTPad_2.0x2.0mm_Drill1.0mm
TP13: -12V; TestPoint_THTPad_2.0x2.0mm_Drill1.0mm
U7: TL072; SOIC-8_3.9x4.9mm_P1.27mm; LCSC C6961

Connections:
-5V: R40.2, TP11.1, U7.1; also elsewhere on the board
GND: C21.2, C22.1, C23.2, C24.1, J3.3, J3.4, J3.5, J3.6, J3.7, J3.8, J4.1, J4.2, J5.1, J5.3, J5.4, J5.6, U7.3 (+), U7.5 (+); also elsewhere on the board
unnamed: D6.2 (A), J3.9, J3.10
unnamed: D7.1 (K), J3.1, J3.2
unnamed: R39.2, R40.1, U7.2 (-)
unnamed: U7.6 (-), U7.7

Notes on the sheet:
UI power connection
Eurorack PSU connection
Used for VCO current source

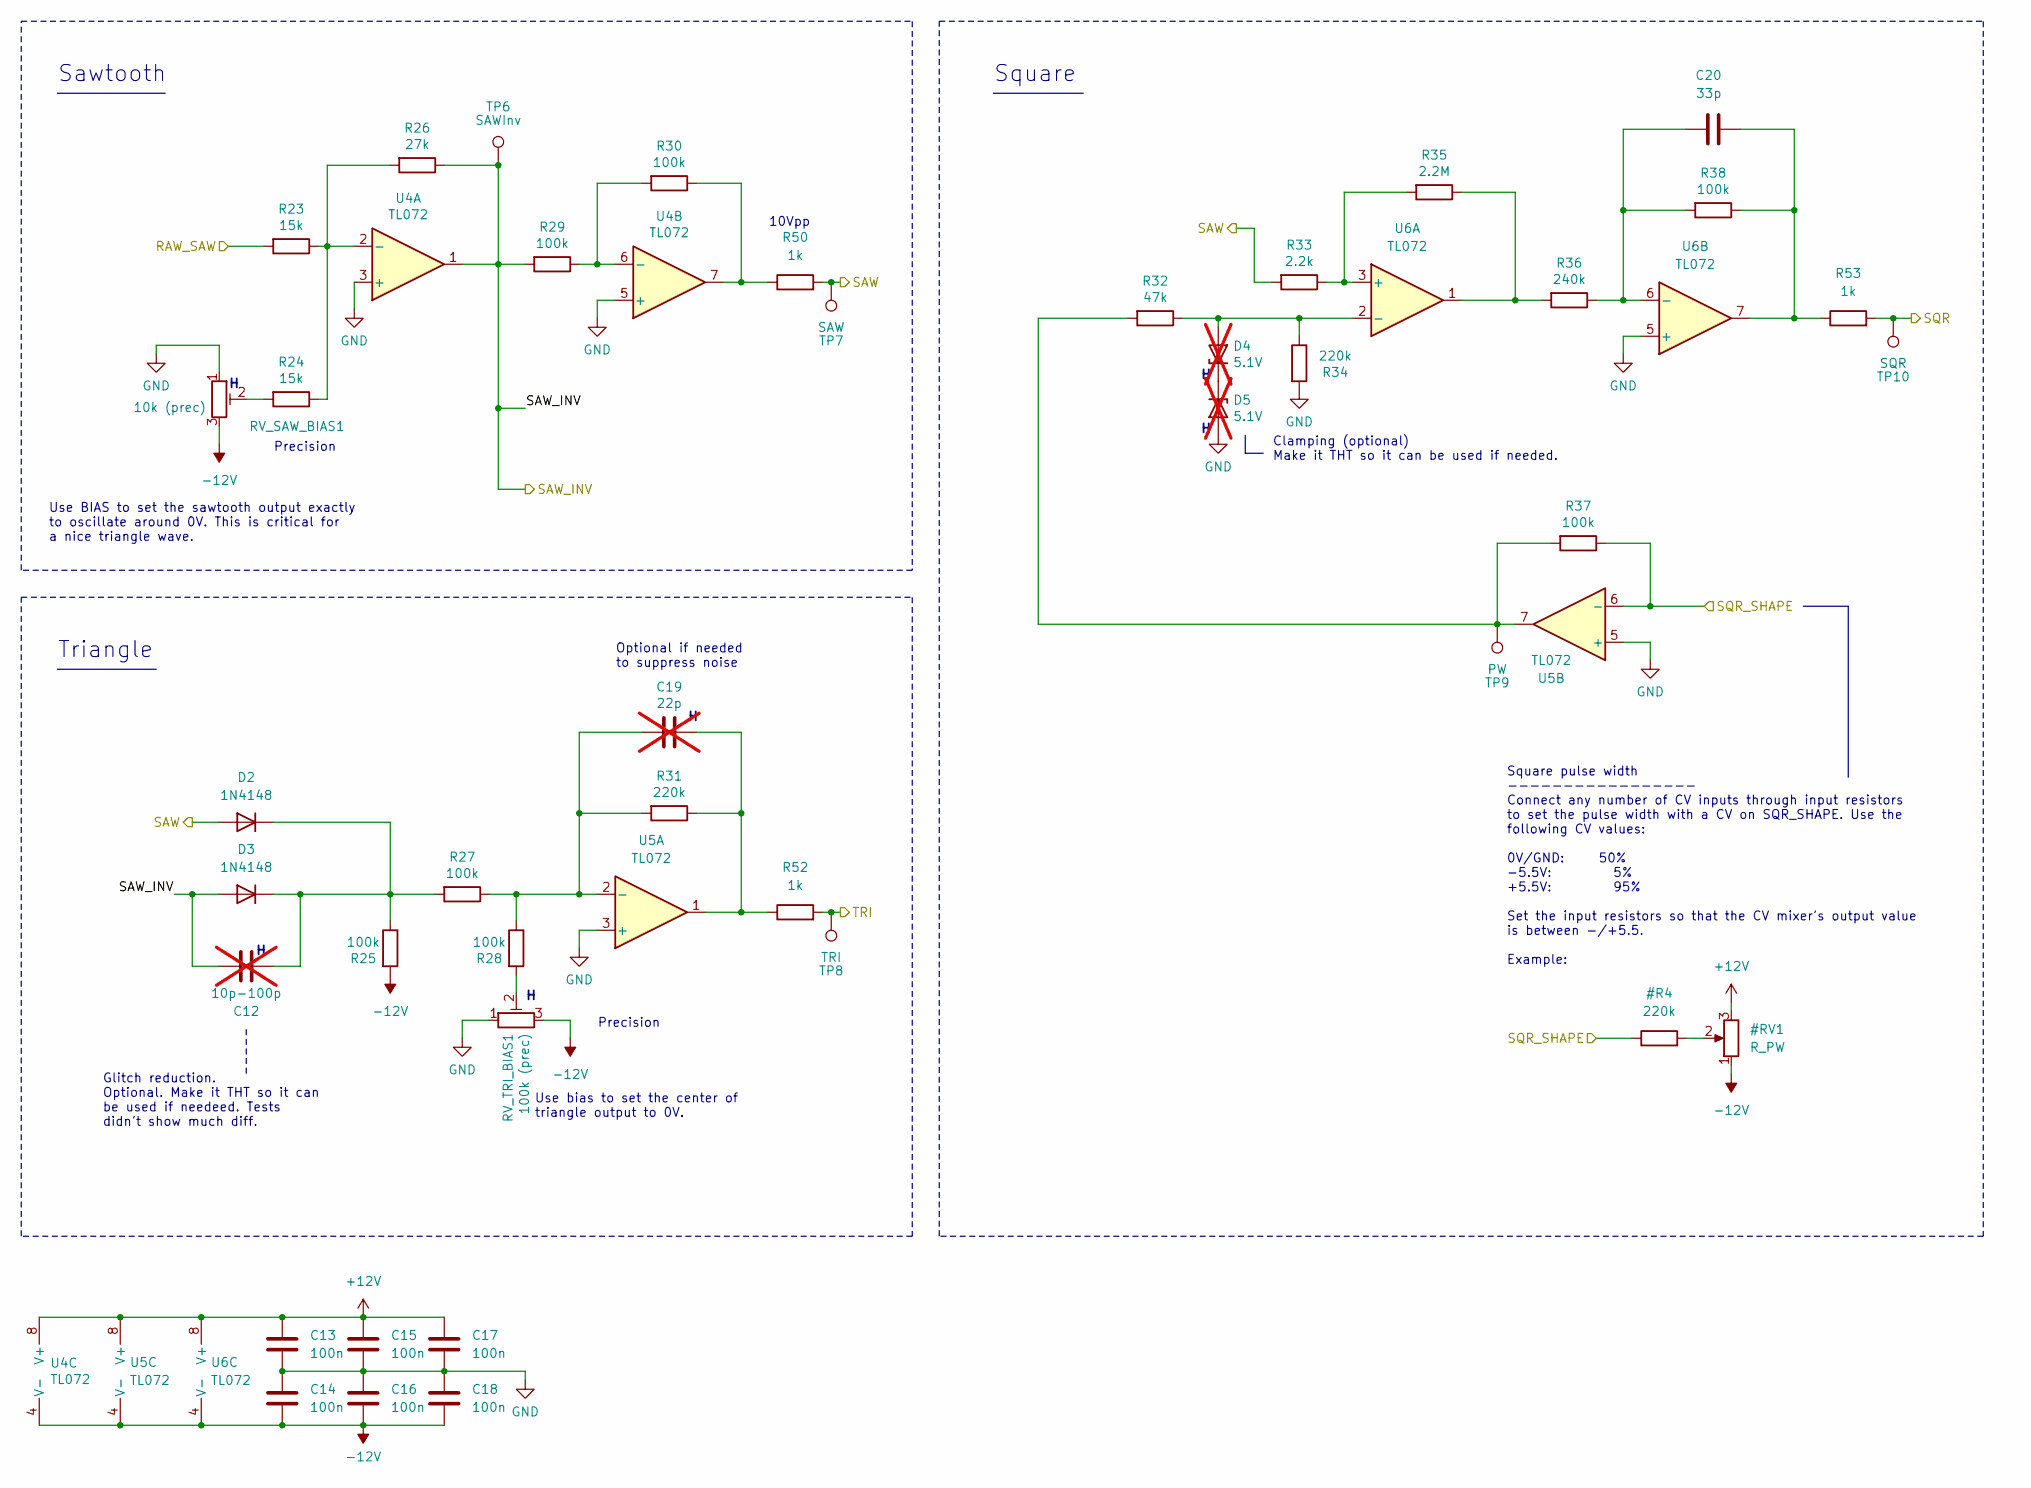
[picture p62: schematic waveshapers.kicad_sch]

Parts:
C12: 10p-100p; C_Rect_L7.0mm_W2.5mm_P5.00mm; not fitted
C13, C14, C15, C16, C17, C18: 100n; C_0603_1608Metric; LCSC C14663
C19: 22p; C_Disc_D3.0mm_W2.0mm_P2.50mm; not fitted
C20: 33p; C_0603_1608Metric; LCSC C1663
D2, D3: 1N4148; D_SOD-123; LCSC C81598
D4, D5: 5.1V; D_DO-34_SOD68_P2.54mm_Vertical_AnodeUp; not fitted
R23, R24: 15k; R_0603_1608Metric; LCSC C22809
R25, R27, R28, R29, R30, R37, R38: 100k; R_0603_1608Metric; LCSC C25803
R26: 27k; R_0603_1608Metric; LCSC C22967
R31, R34: 220k; R_0603_1608Metric; LCSC C22961
R32: 47k; R_0603_1608Metric; LCSC C25819
R33: 2.2k; R_0603_1608Metric; LCSC C4190
R35: 2.2M; R_0603_1608Metric; LCSC C22938
R36: 240k; R_0603_1608Metric; LCSC C4197
R50, R52, R53: 1k; R_0603_1608Metric; LCSC C21190
RV_SAW_BIAS1: 10k (prec); Potentiometer_Bourns_3006P_Horizontal; Mouser Part no. 652-3006P-1-103-LF
RV_TRI_BIAS1: 100k (prec); Potentiometer_Bourns_3006P_Horizontal; Mouser Part no. 652-3006P-1-104-LF
TP6: SAWInv; TestPoint_THTPad_2.0x2.0mm_Drill1.0mm
TP7: SAW; TestPoint_THTPad_2.0x2.0mm_Drill1.0mm
TP8: TRI; TestPoint_THTPad_2.0x2.0mm_Drill1.0mm
TP9: PW; TestPoint_THTPad_2.0x2.0mm_Drill1.0mm
TP10: SQR; TestPoint_THTPad_2.0x2.0mm_Drill1.0mm
U4, U5, U6: TL072; SOIC-8_3.9x4.9mm_P1.27mm; LCSC C6961

Connections:
GND: C13.2, C14.1, C15.2, C16.1, C17.2, C18.1, D5.2 (A), R34.2, RV_SAW_BIAS1.1, RV_TRI_BIAS1.1, U4.3 (+), U4.5 (+), U5.3 (+), U5.5 (+), U6.5 (+); also elsewhere on the board
unnamed: C19.1, R31.1, R52.1, U5.1
unnamed: C20.2, R38.1, R53.1, U6.7
unnamed: C12.1, D2.1 (K), D3.1 (K), R25.1, R27.2
unnamed: D4.2 (A), R32.1, R34.1, U6.2 (-)
unnamed: D4.1 (K), D5.1 (K)
unnamed: R24.2, RV_SAW_BIAS1.2
unnamed: R28.2, RV_TRI_BIAS1.2
unnamed: R30.1, R50.1, U4.7
unnamed: R32.2, R37.2, TP9.1, U5.7
unnamed: R35.1, R36.2, U6.1
unnamed: R23.1, R24.1, R26.2, U4.2 (-)
unnamed: R29.1, R30.2, U4.6 (-)
unnamed: C19.2, R27.1, R28.1, R31.2, U5.2 (-)
unnamed: R33.1, R35.2, U6.3 (+)
unnamed: C20.1, R36.1, R38.2, U6.6 (-)
RAW_SAW: R23.2; also elsewhere on the board
SAW: D2.2 (A), R33.2, R50.2, TP7.1; also elsewhere on the board
SAW_INV: C12.2, D3.2 (A), R26.1, R29.2, TP6.1, U4.1; also elsewhere on the board
SQR: R53.2, TP10.1; also elsewhere on the board
TRI: R52.2, TP8.1; also elsewhere on the board

Notes on the sheet:
Use bias to set the center of triangle output to 0V.
Clamping (optional) Make it THT so it can be used if needed.
Use BIAS to set the sawtooth output exactly to oscillate around 0V. This is critical for a nice triangle wave.
Sawtooth
Precision
10Vpp
Square pulse width ----------------- Connect any number of CV inputs through input resistors to set the pulse width with a CV on SQR_SHAPE. Use the following CV values: 0V/GND: 50% -5.5V: 5% +5.5V: 95% Set the input resistors so that the CV mixer's output value is between -/+5.5. Example:
Square
Optional if needed to suppress noise
Glitch reduction. Optional. Make it THT so it can be used if needeed. Tests didn't show much diff.
Triangle
