shmoergh/hog-moduleur/02-vco/electronics/core/vco-core.kicad_pcb

## KiCad design 02-vco/electronics/core/vco-core.kicad_pcb (continued)

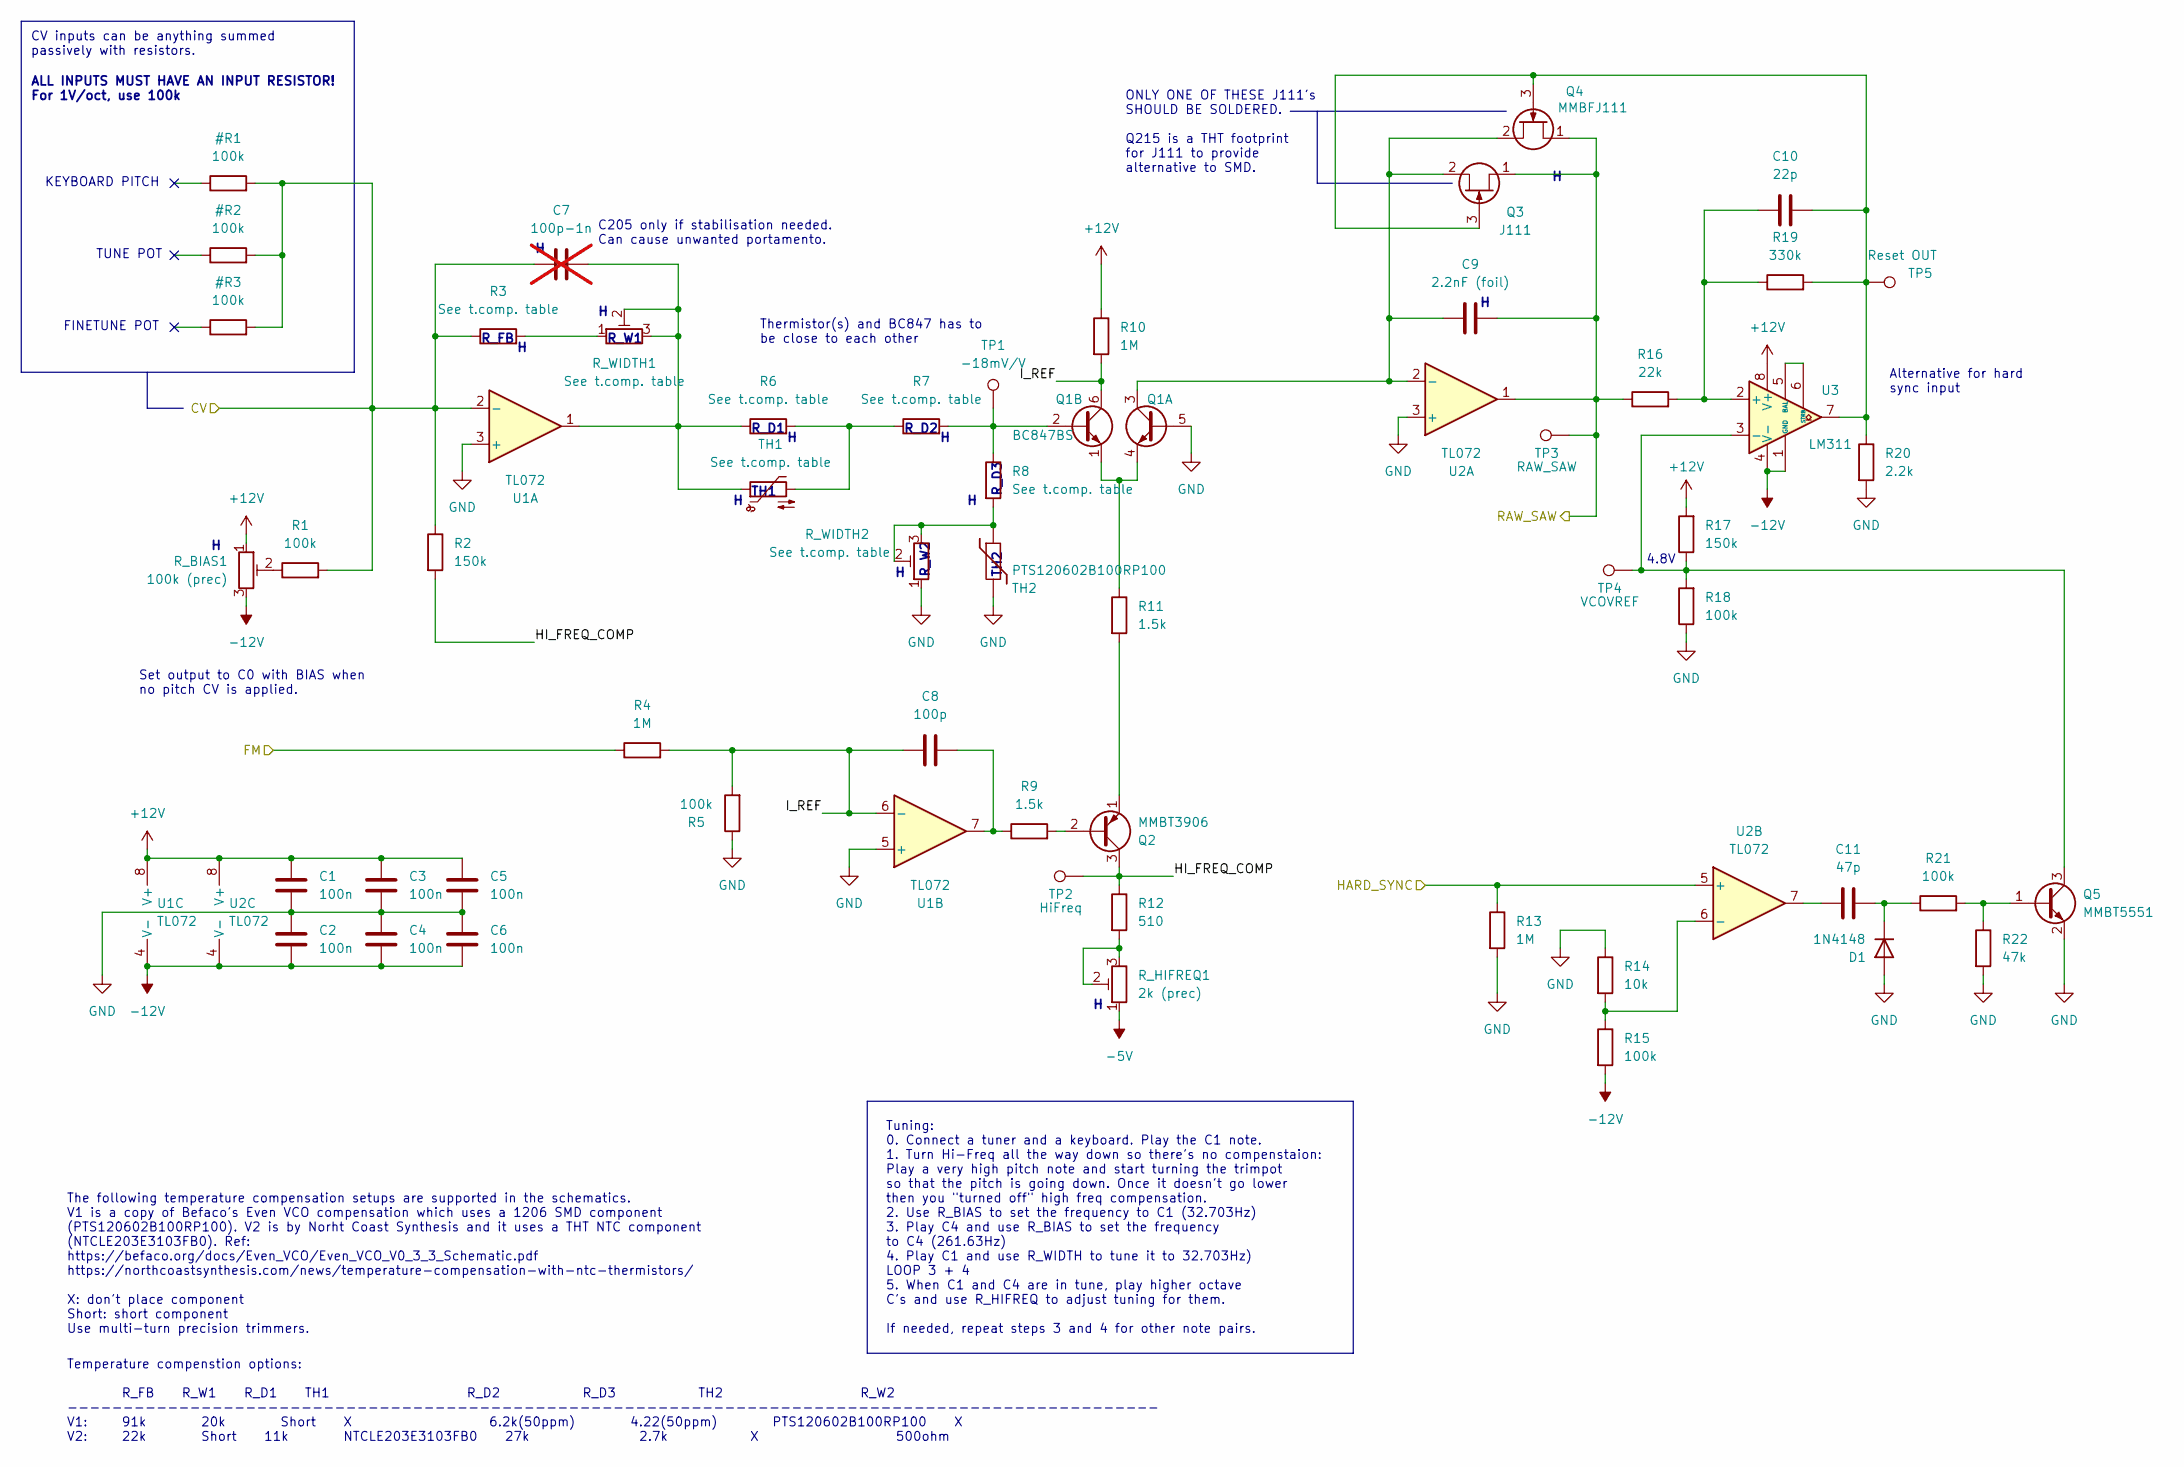
[picture p63: schematic raw-oscillator.kicad_sch]

Parts:
C1, C2, C3, C4, C5, C6: 100n; C_0603_1608Metric; LCSC C14663
C7: 100p-1n; C_Disc_D3.0mm_W1.6mm_P2.50mm; not fitted
C8: 100p; C_0603_1608Metric; LCSC C14858
C9: 2.2nF (foil); C_Rect_L7.2mm_W2.5mm_P5.00mm_FKS2_FKP2_MKS2_MKP2; Mouser Part no. 80-R82MC1220AA50J
C10: 22p; C_0603_1608Metric; LCSC C1653
C11: 47p; C_0603_1608Metric; LCSC C1671
D1: 1N4148; D_SOD-123; LCSC C81598
Q1: BC847BS; SOT-363_SC-70-6; LCSC C5380687
Q2: MMBT3906; SOT-23_Handsoldering; LCSC C7420354
Q3: J111; TO-92_Inline_Wide; Mouser Part no. 512-J111
Q4: MMBFJ111; SOT-23; LCSC C274688
Q5: MMBT5551; SOT-23; LCSC C2145
R1, R5, R15, R18, R21: 100k; R_0603_1608Metric; LCSC C25803
R2, R17: 150k; R_0603_1608Metric; LCSC C22807
R3, R6, R7, R8: See t.comp. table; R_Axial_DIN0207_L6.3mm_D2.5mm_P7.62mm_Horizontal
R4, R10, R13: 1M; R_0603_1608Metric; LCSC C22935
R9, R11: 1.5k; R_0603_1608Metric; LCSC C22843
R12: 510; R_0603_1608Metric; LCSC C23193
R14: 10k; R_0603_1608Metric; LCSC C25804
R16: 22k; R_0603_1608Metric; LCSC C31850
R19: 330k; R_0603_1608Metric; LCSC C23137
R20: 2.2k; R_0603_1608Metric; LCSC C4190
R22: 47k; R_0603_1608Metric; LCSC C25819
R_BIAS1: 100k (prec); Potentiometer_Bourns_3006P_Horizontal; Mouser Part no. 652-3006P-1-104-LF
R_HIFREQ1: 2k (prec); Potentiometer_Bourns_3006P_Horizontal; Mouser Part no. 652-3006P-1-202-LF
R_WIDTH1: See t.comp. table; Potentiometer_Bourns_3006P_Horizontal; Mouser Part no. 652-3006P-7-203-LF
R_WIDTH2: See t.comp. table; Potentiometer_Bourns_3006P_Horizontal; Mouser Part no. 652-3006P-1-501-LF
TH1: See t.comp. table; TO-92-2; Mouser Part no. 594-2381-640-55103
TH2: PTS120602B100RP100; R_1206_3216Metric_Pad1.30x1.75mm_HandSolder; Mouser Part no. 594-PTS120601B100RP
TP1: -18mV/V; TestPoint_THTPad_2.0x2.0mm_Drill1.0mm
TP2: HiFreq; TestPoint_THTPad_2.0x2.0mm_Drill1.0mm
TP3: RAW_SAW; TestPoint_THTPad_2.0x2.0mm_Drill1.0mm
TP4: VCOVREF; TestPoint_THTPad_2.0x2.0mm_Drill1.0mm
TP5: Reset OUT; TestPoint_THTPad_2.0x2.0mm_Drill1.0mm
U1, U2: TL072; SOIC-8_3.9x4.9mm_P1.27mm; LCSC C6961
U3: LM311; SOIC-8_3.9x4.9mm_P1.27mm; LCSC C12597

Connections:
-5V: R_HIFREQ1.1; also elsewhere on the board
/Raw oscillator/HI_FREQ_COMP: Q2.3 (C), R2.2, R12.1, TP2.1
/Raw oscillator/I_REF: C8.1, Q1.6 (C1), R4.2, R5.2, R10.2, U1.6 (-)
CV: C7.1, R1.2, R2.1, R3.1, U1.2 (-); also elsewhere on the board
FM: R4.1; also elsewhere on the board
GND: C1.2, C2.1, C3.2, C4.1, C5.2, C6.1, D1.2 (A), Q1.5 (B2), Q5.2 (E), R5.1, R13.2, R14.1, R18.1, R20.2, R22.2, R_WIDTH2.1, TH2.2, U1.3 (+), U1.5 (+), U2.3 (+); also elsewhere on the board
HARD_SYNC: R13.1, U2.5 (+); also elsewhere on the board
unnamed: C7.2, R6.1, R_WIDTH1.2, R_WIDTH1.3, TH1.1, U1.1
unnamed: C8.2, R9.1, U1.7
unnamed: C11.1, U2.7
unnamed: C11.2, D1.1 (K), R21.1
unnamed: Q1.2 (B1), R7.2, R8.1, TP1.1
unnamed: Q1.1 (E1), Q1.4 (E2), R11.1
unnamed: C9.1, Q1.3 (C2), Q3.2 (S), Q4.2 (S), U2.2 (-)
unnamed: Q2.2 (B), R9.2
unnamed: Q2.1 (E), R11.2
unnamed: C10.2, Q3.3 (G), Q4.3 (G), R19.2, R20.1, TP5.1, U3.7
unnamed: Q5.1 (B), R21.2, R22.1
unnamed: Q5.3 (C), R17.1, R18.2, TP4.1, U3.3 (-)
unnamed: R1.1, R_BIAS1.2
unnamed: R3.2, R_WIDTH1.1
unnamed: R6.2, R7.1, TH1.2
unnamed: R8.2, R_WIDTH2.2, R_WIDTH2.3, TH2.1
unnamed: R12.2, R_HIFREQ1.2, R_HIFREQ1.3
unnamed: R14.2, R15.1, U2.6 (-)
unnamed: C10.1, R16.2, R19.1, U3.2 (+)
unnamed: U3.5 (BAL), U3.6 (STRB)
RAW_SAW: C9.2, Q3.1 (D), Q4.1 (D), R16.1, TP3.1, U2.1; also elsewhere on the board

Notes on the sheet:
ONLY ONE OF THESE J111's SHOULD BE SOLDERED. Q215 is a THT footprint for J111 to provide alternative to SMD.
R_W2
TH2
Tuning: 0. Connect a tuner and a keyboard. Play the C1 note. 1. Turn Hi-Freq all the way down so there's no compenstaion: Play a very high pitch note and start turning the trimpot so that the pitch is going down. Once it doesn't go lower then you "turned off" high freq compensation. 2. Use R_BIAS t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
R_W1
C205 only if stabilisation needed. Can cause unwanted portamento.
Thermistor(s) and BC847 has to be close to each other
ALL INPUTS MUST HAVE AN INPUT RESISTOR! For 1V/oct, use 100k
Alternative for hard sync input
Temperature compenstion options: R_FB R_W1 R_D1 TH1 R_D2 R_D3 TH2 R_W2 -------------------------------------------------------------------------------------------------- V1: 91k 20k Short X 6.2k(50ppm) 4.22(50ppm) PTS120602B100RP100 X V2: 22k Short 11k NTCLE203E3103FB0 27k 2.7k X 500ohm
CV inputs can be anything summed passively with resistors.
KEYBOARD PITCH
TUNE POT
The following temperature compensation setups are supported in the schematics. V1 is a copy of Befaco's Even VCO compensation which uses a 1206 SMD component (PTS120602B100RP100). V2 is by Norht Coast Synthesis and it uses a THT NTC component (NTCLE203E3103FB0). Ref: https://befaco.org/docs/Even_VC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
TH1
R_FB
FINETUNE POT
R_D3
R_D1
Set output to C0 with BIAS when no pitch CV is applied.
R_D2
4.8V

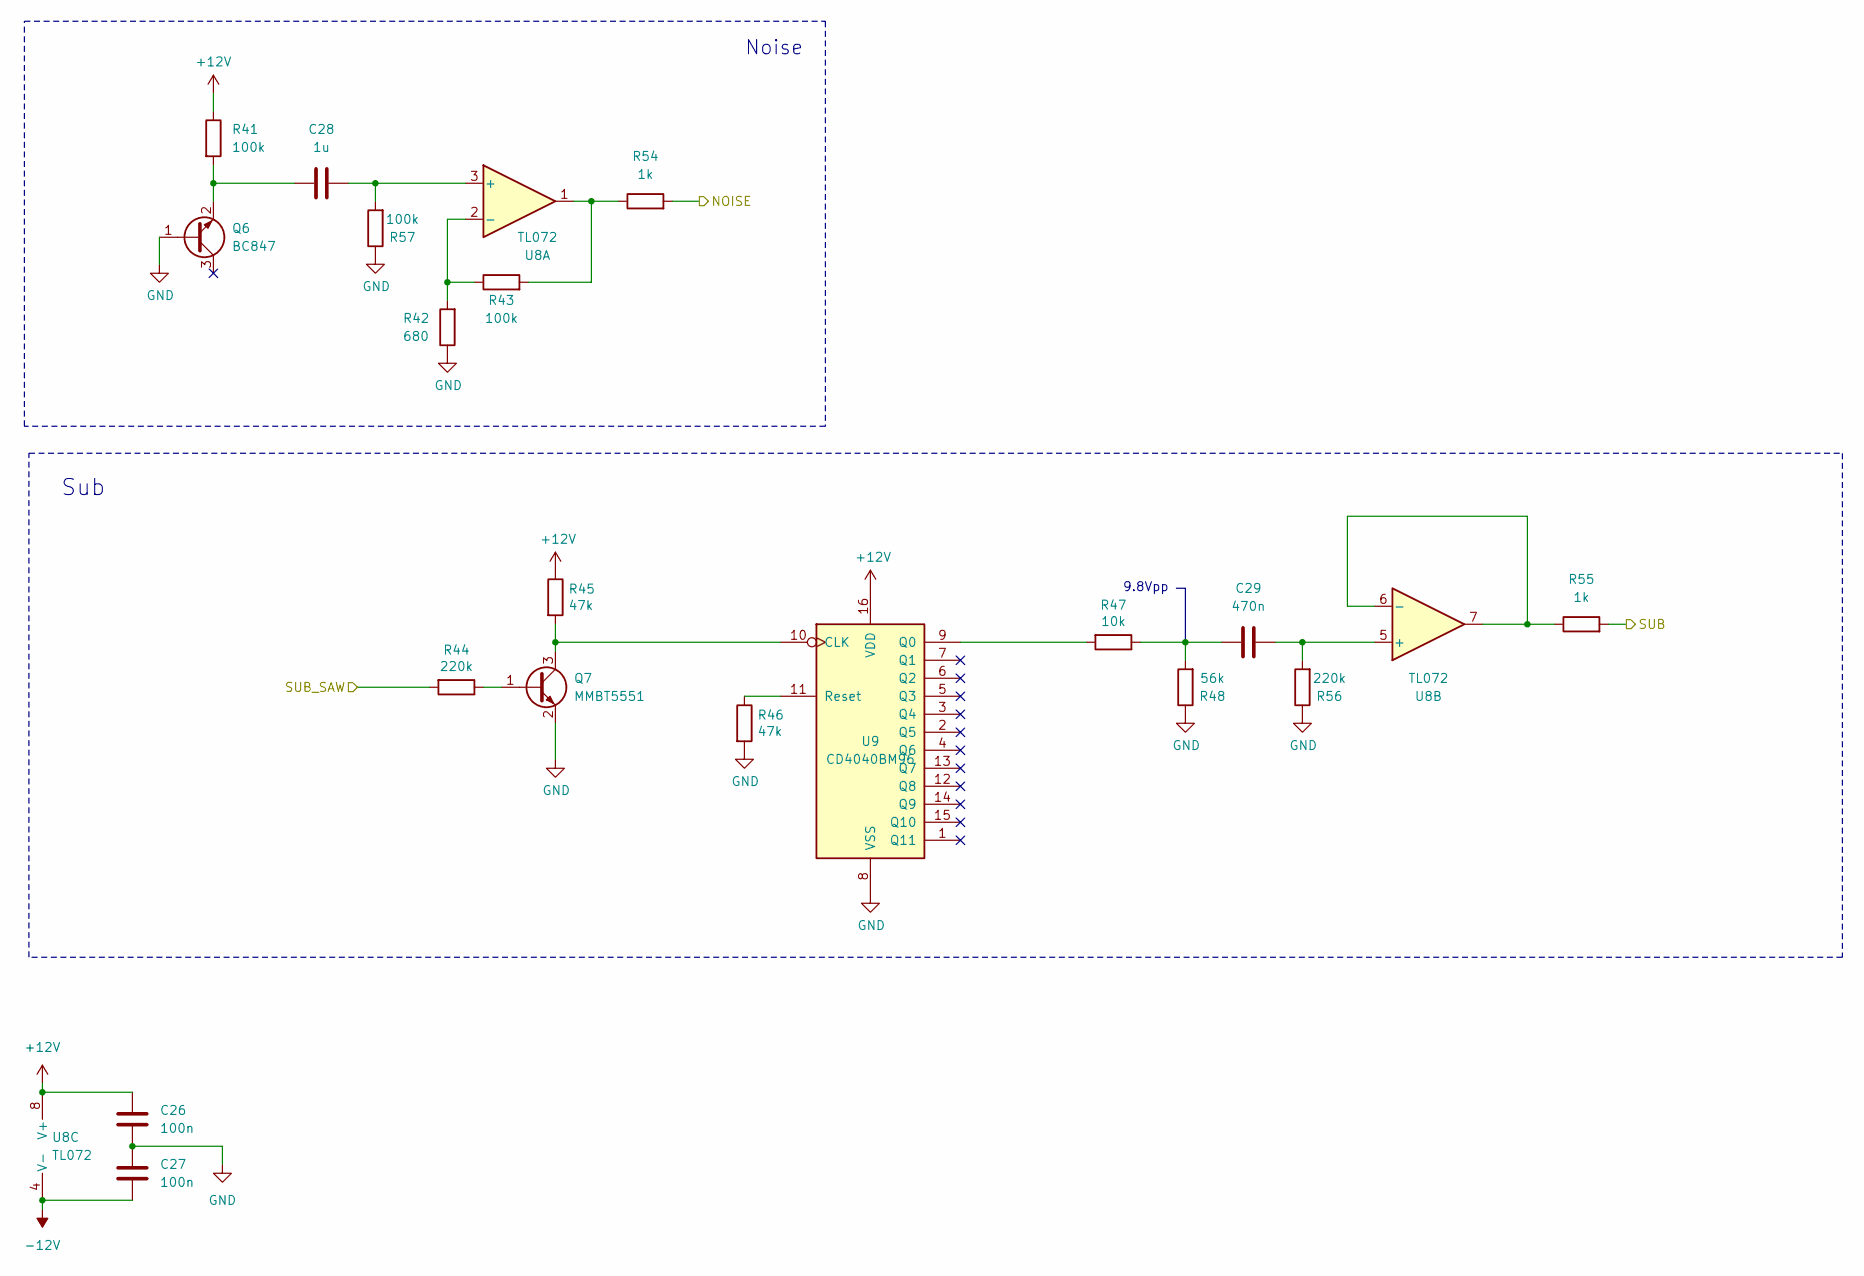
[picture p64: schematic sub+noise.kicad_sch]

Parts:
C26, C27: 100n; C_0603_1608Metric; LCSC C14663
C28: 1u; C_0603_1608Metric; LCSC C15849
C29: 470n; C_Rect_L7.2mm_W3.5mm_P5.00mm_FKS2_FKP2_MKS2_MKP2; Mouser Part no. 80-R82DC3470DQ60K
Q6: BC847; SOT-23; LCSC C8664
Q7: MMBT5551; SOT-23; LCSC C2145
R41, R43, R57: 100k; R_0603_1608Metric; LCSC C25803
R42: 680; R_0603_1608Metric; LCSC C23228
R44, R56: 220k; R_0603_1608Metric; LCSC C22961
R45, R46: 47k; R_0603_1608Metric; LCSC C25819
R47: 10k; R_0603_1608Metric; LCSC C25804
R48: 56k; R_0603_1608Metric; LCSC C23206
R54, R55: 1k; R_0603_1608Metric; LCSC C21190
U8: TL072; SOIC-8_3.9x4.9mm_P1.27mm; LCSC C6961
U9: CD4040BM96; SOIC-16_3.9x9.9mm_P1.27mm; LCSC C353974

Connections:
GND: C26.2, C27.1, Q6.1 (B), Q7.2 (E), R42.1, R46.2, R48.1, R56.1, R57.1, U9.8 (VSS); also elsewhere on the board
NOISE: R54.2; also elsewhere on the board
unnamed: C29.1, R47.1, R48.2
unnamed: C28.1, Q6.2 (E), R41.2
unnamed: Q7.1 (B), R44.1
unnamed: Q7.3 (C), R45.2, U9.10 (CLK)
unnamed: R43.2, R54.1, U8.1
unnamed: C28.2, R57.2, U8.3 (+)
unnamed: R42.2, R43.1, U8.2 (-)
unnamed: C29.2, R56.2, U8.5 (+)
unnamed: R55.1, U8.6 (-), U8.7
unnamed: R47.2, U9.9 (Q0)
unnamed: R46.1, U9.11 (Reset)
SAW: R44.2; also elsewhere on the board
SUB: R55.2; also elsewhere on the board

Notes on the sheet:
Noise
9.8Vpp
Sub

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
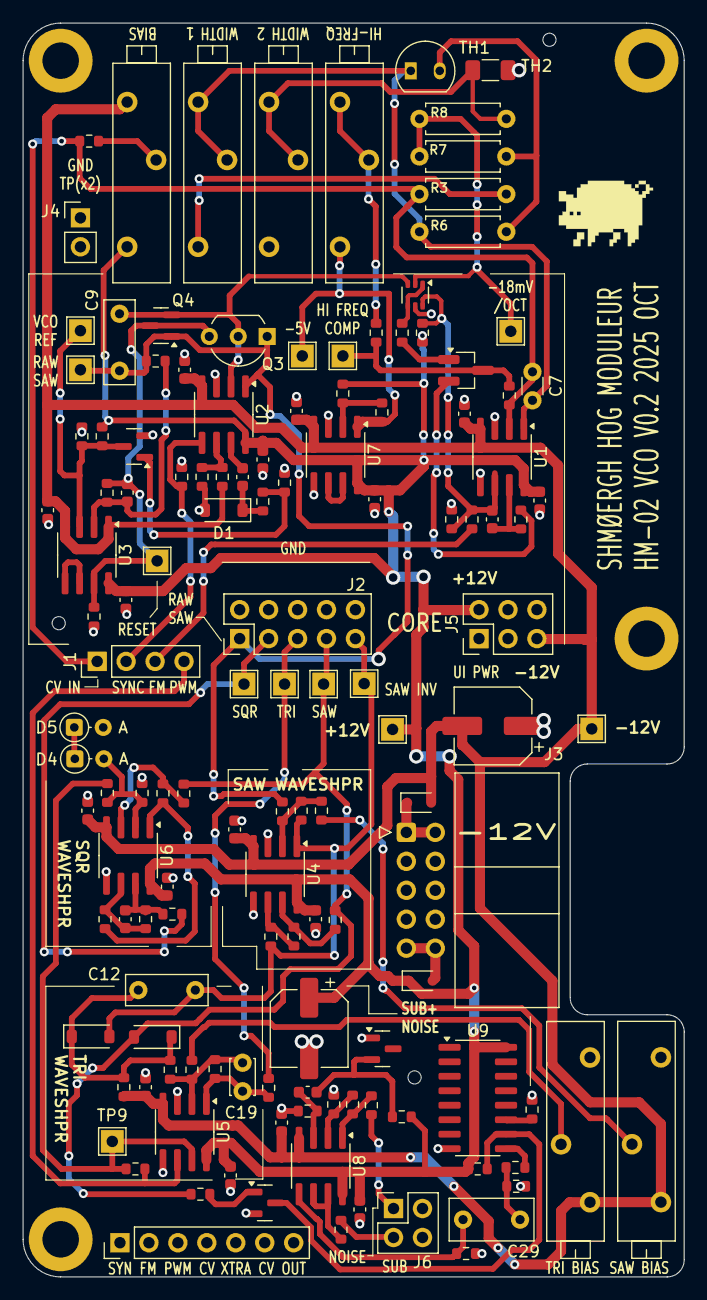
[picture p65: board vco-core.kicad_pcb from above]

Board: 2 copper layers, 58.0 x 110.0 mm, 138 parts (0 on the bottom side), 67 nets.
