shmoergh/hog-moduleur/02-vco/electronics/ui-octave-switch/vco-ui.kicad_pcb

## KiCad design 02-vco/electronics/ui-octave-switch/vco-ui.kicad_pcb (2025-10-25)

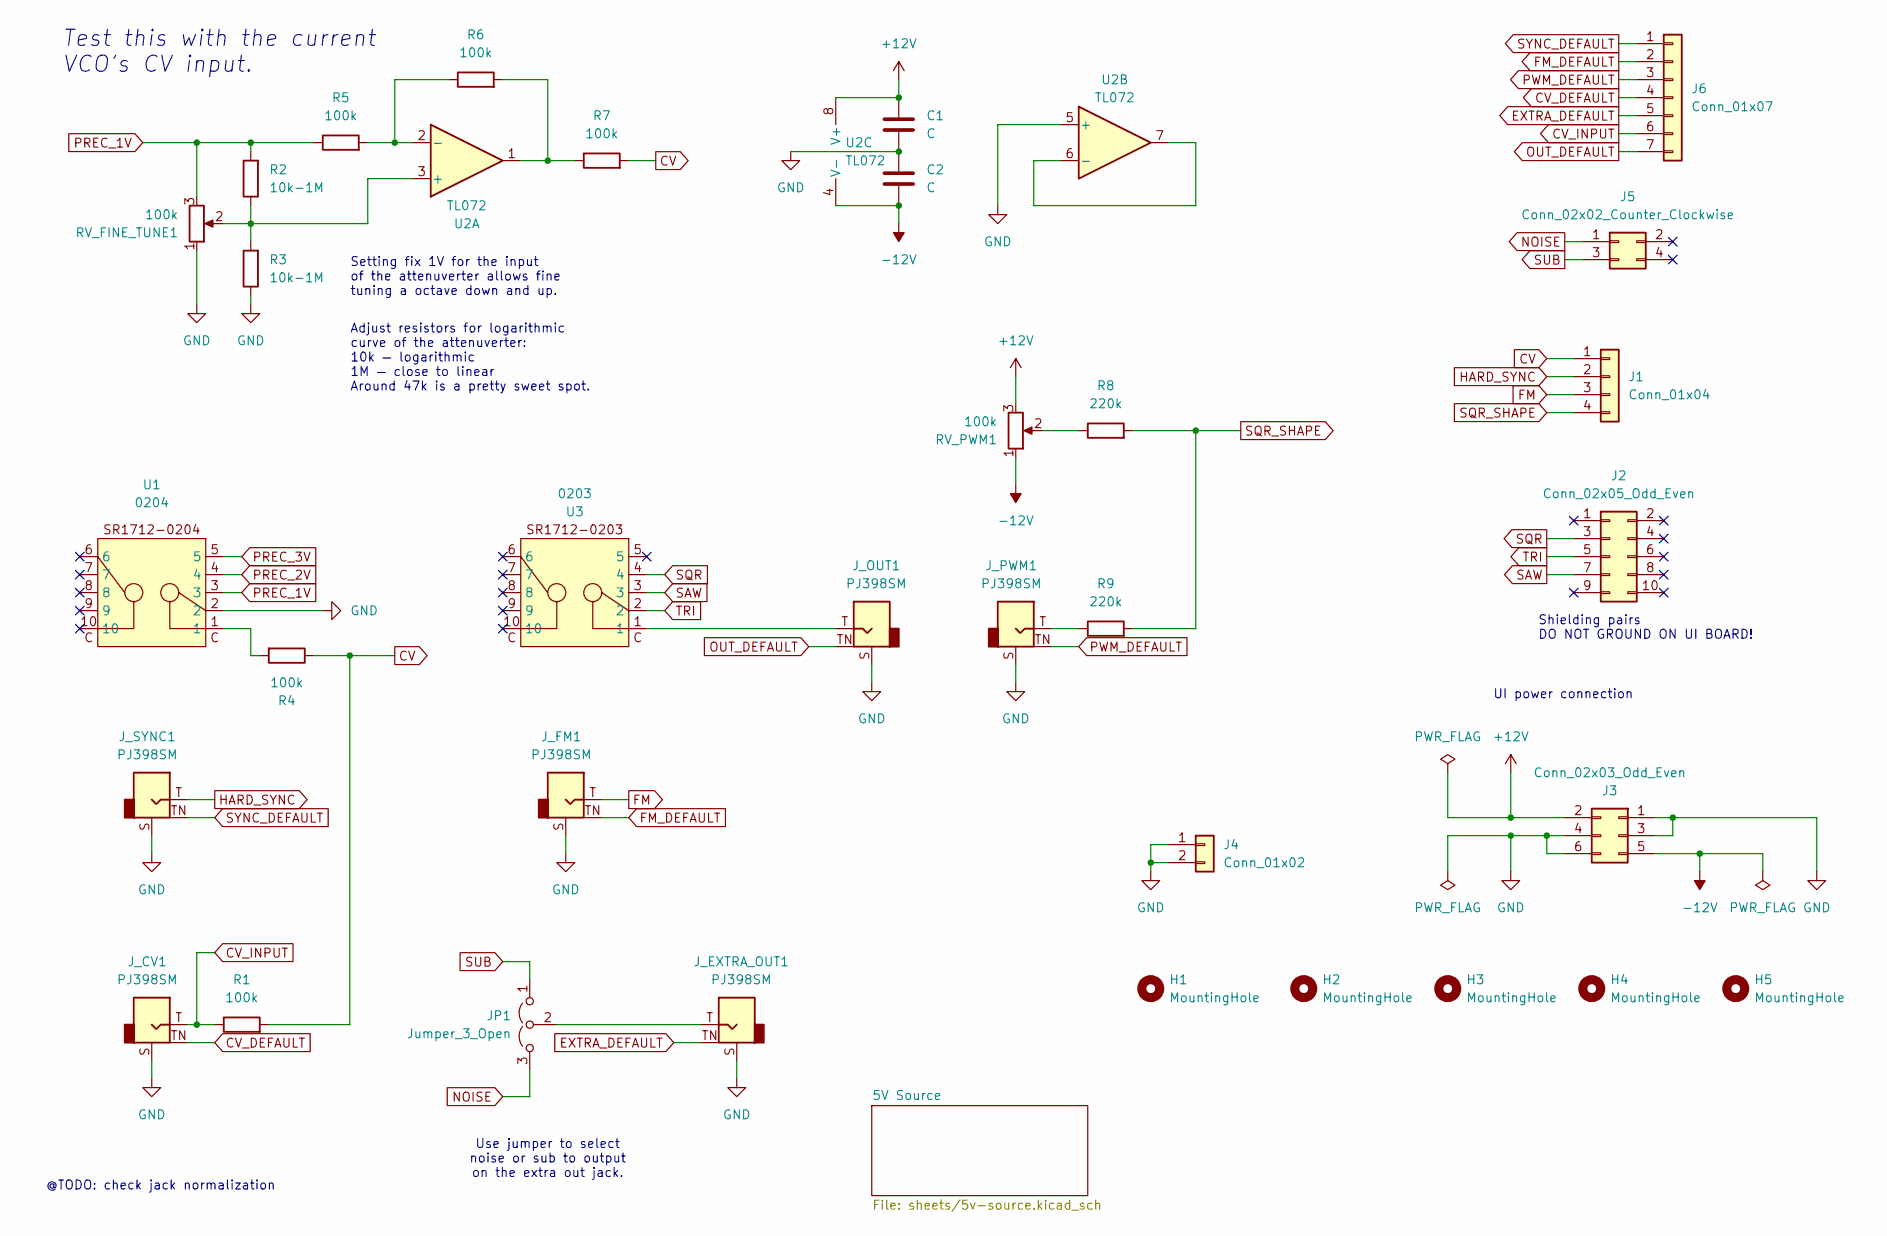
[picture p66: schematic vco-ui.kicad_sch, Hog Moduleur VCO UI]

Parts:
C1, C2: C; C_Disc_D5.0mm_W2.5mm_P2.50mm
H1, H2, H3, H4, H5: MountingHole; MountingHole_3.2mm_M3_DIN965_Pad
J1: Conn_01x04; PinSocket_1x04_P2.54mm_Vertical; Part no. 200-SSW10401TMS
J2: Conn_02x05_Odd_Even; PinSocket_2x05_P2.54mm_Vertical; Part no. 200-SSW10501TD
J3: Conn_02x03_Odd_Even; PinSocket_2x03_P2.54mm_Vertical; Part no. 200-SSW10301TD
J4: Conn_01x02; PinSocket_1x02_P2.54mm_Vertical; Part no. 200-SSW10201TS
J5: Conn_02x02_Counter_Clockwise; PinSocket_2x02_P2.54mm_Vertical; Part no. 200-SSW10206TD
J6: Conn_01x07; PinSocket_1x07_P2.54mm_Vertical; Part no. 200-SSW10601TS
JP1: Jumper_3_Open; PinHeader_1x03_P2.54mm_Horizontal; Part no. 200-HTSW10308TSRA
J_CV1: PJ398SM; Jack_3.5mm_QingPu_WQP-PJ398SM_Vertical_CircularHoles; Part no. PJ398SM
J_EXTRA_OUT1: PJ398SM; Jack_3.5mm_QingPu_WQP-PJ398SM_Vertical_CircularHoles; Part no. PJ398SM
J_FM1: PJ398SM; Jack_3.5mm_QingPu_WQP-PJ398SM_Vertical_CircularHoles; Part no. PJ398SM
J_OUT1: PJ398SM; Jack_3.5mm_QingPu_WQP-PJ398SM_Vertical_CircularHoles; Part no. PJ398SM
J_PWM1: PJ398SM; Jack_3.5mm_QingPu_WQP-PJ398SM_Vertical_CircularHoles; Part no. PJ398SM
J_SYNC1: PJ398SM; Jack_3.5mm_QingPu_WQP-PJ398SM_Vertical_CircularHoles; Part no. PJ398SM
R1, R4, R5, R6, R7: 100k; R_Axial_DIN0207_L6.3mm_D2.5mm_P7.62mm_Horizontal; Part no. 603-MFR-25FRF52100K
R2, R3: 10k-1M; R_Axial_DIN0207_L6.3mm_D2.5mm_P7.62mm_Horizontal; Part no. 603-MFR-25FRF52100K
R8, R9: 220k; R_Axial_DIN0207_L6.3mm_D2.5mm_P7.62mm_Horizontal; Part no. 603-MFR-25FRF52-220K
RV_FINE_TUNE1: 100k; Potentiometer_Bourns_Single-PTV09A; Part no. 652-PTV09A4025FB104
RV_PWM1: 100k; Potentiometer_Bourns_Single-PTV09A; Part no. 652-PTV09A4025FB104
U1: 0204; SR1712-0204
U2: TL072; DIP-8_W7.62mm_LongPads
U3: 0203; SR1712-0203; Part no. 105-SR1712F-23NS

Connections:
+12V: C1.1, J3.2, RV_PWM1.3, U2.8 (V+); also elsewhere on the board
-12V: C2.2, J3.5, RV_PWM1.1, U2.4 (V-)
CV: J1.1, R1.2, R4.1, R7.2
CV_DEFAULT: J6.4, J_CV1.TN
CV_INPUT: J6.6, J_CV1.T, R1.1
EXTRA_DEFAULT: J6.5, J_EXTRA_OUT1.TN
FM: J1.3, J_FM1.T
FM_DEFAULT: J6.2, J_FM1.TN
GND: C1.2, C2.1, J3.1, J3.3, J3.4, J3.6, J4.1, J4.2, J_CV1.S, J_EXTRA_OUT1.S, J_FM1.S, J_OUT1.S, J_PWM1.S, J_SYNC1.S, R3.1, RV_FINE_TUNE1.1, U1.2, U2.5 (+); also elsewhere on the board
HARD_SYNC: J1.2, J_SYNC1.T
NOISE: J5.1, JP1.3 (B)
unnamed: JP1.2 (C), J_EXTRA_OUT1.T
unnamed: J_OUT1.T, U3.1
unnamed: J_PWM1.T, R9.1
unnamed: R4.2, U1.1
unnamed: R6.2, R7.1, U2.1
unnamed: R8.1, RV_PWM1.2
unnamed: R2.1, R3.2, RV_FINE_TUNE1.2, U2.3 (+)
unnamed: R5.2, R6.1, U2.2 (-)
unnamed: U2.6 (-), U2.7
OUT_DEFAULT: J6.7, J_OUT1.TN
PREC_1V: R2.2, R5.1, RV_FINE_TUNE1.3, U1.3; also elsewhere on the board
PREC_2V: U1.4; also elsewhere on the board
PREC_3V: U1.5; also elsewhere on the board
PWM_DEFAULT: J6.3, J_PWM1.TN
SAW: J2.7, U3.3
SQR: J2.3, U3.4
SQR_SHAPE: J1.4, R8.2, R9.2
SUB: J5.3, JP1.1 (A)
SYNC_DEFAULT: J6.1, J_SYNC1.TN
TRI: J2.5, U3.2

Notes on the sheet:
Test this with the current VCO's CV input.
Setting fix 1V for the input of the attenuverter allows fine tuning a octave down and up.
@TODO: check jack normalization
UI power connection
Adjust resistors for logarithmic curve of the attenuverter: 10k — logarithmic 1M — close to linear Around 47k is a pretty sweet spot.
Use jumper to select noise or sub to output on the extra out jack.
Shielding pairs DO NOT GROUND ON UI BOARD!

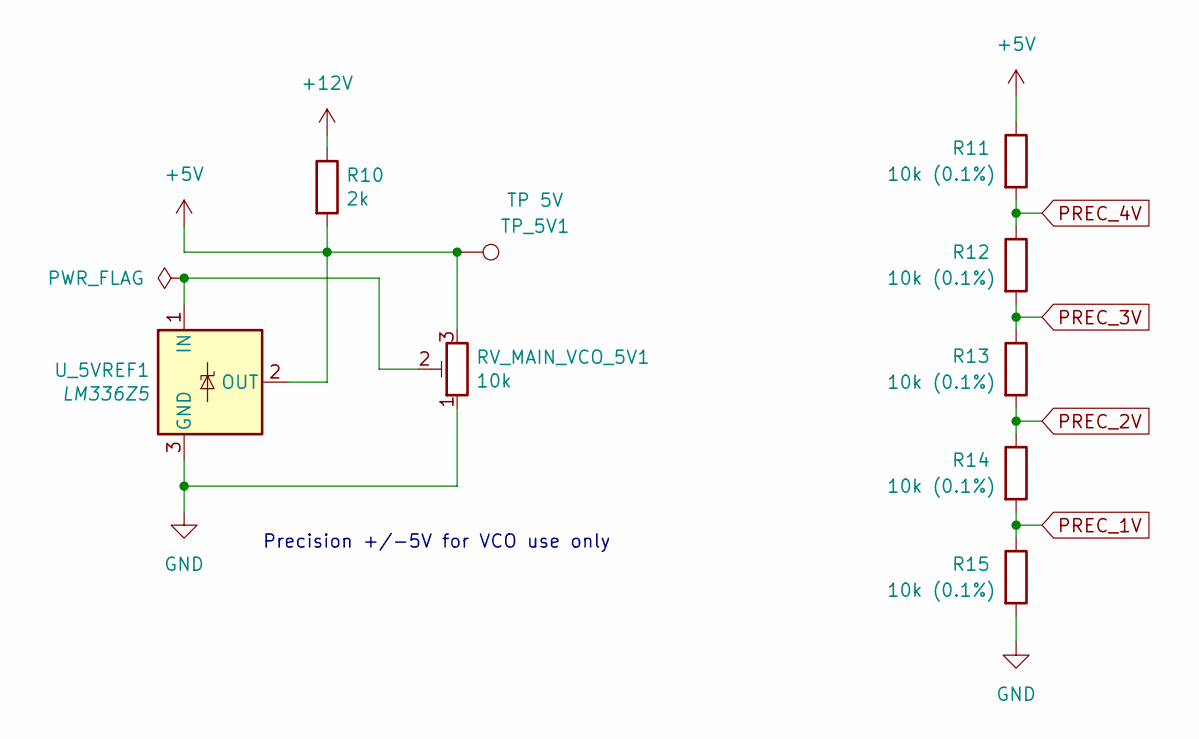
[picture p67: schematic 5v-source.kicad_sch]

Parts:
R10: 2k; R_Axial_DIN0207_L6.3mm_D2.5mm_P7.62mm_Horizontal; Part No. 603-MFR-25FTF52-2K
R11, R12, R13, R14, R15: 10k (0.1%); R_Axial_DIN0207_L6.3mm_D2.5mm_P7.62mm_Horizontal
RV_MAIN_VCO_5V1: 10k; Potentiometer_Bourns_3006P_Horizontal; Part No. 652-3006P-1-103-LF
TP_5V1: TP 5V; TestPoint_THTPad_2.0x2.0mm_Drill1.0mm
U_5VREF1: LM336Z5; TO-92L_Inline_Wide; Part No. 926-LM336Z-50/NOPB

Connections:
+5V: R10.2, R11.1, RV_MAIN_VCO_5V1.3, TP_5V1.1, U_5VREF1.2 (OUT)
+12V: R10.1; also elsewhere on the board
GND: R15.2, RV_MAIN_VCO_5V1.1, U_5VREF1.3 (GND); also elsewhere on the board
unnamed: RV_MAIN_VCO_5V1.2, U_5VREF1.1 (IN)
PREC_1V: R14.2, R15.1; also elsewhere on the board
PREC_2V: R13.2, R14.1; also elsewhere on the board
PREC_3V: R12.2, R13.1; also elsewhere on the board
PREC_4V: R11.2, R12.1

Notes on the sheet:
Precision +/-5V for VCO use only

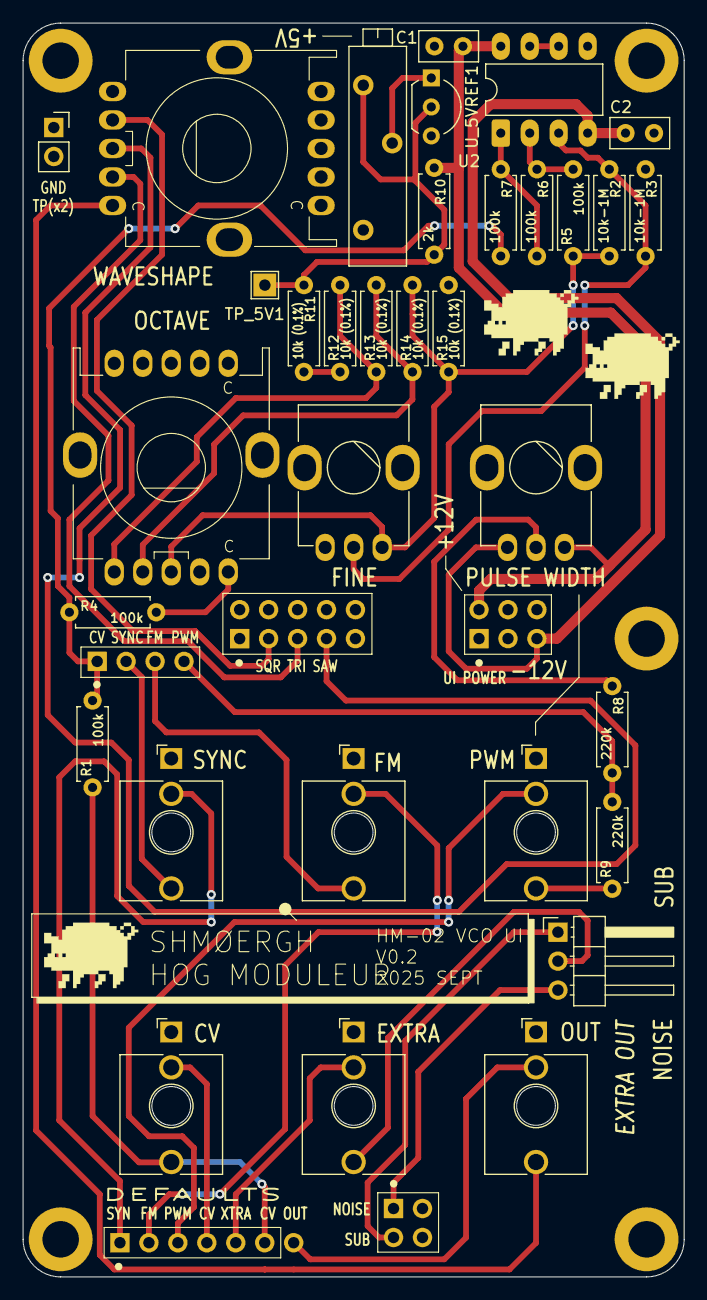
[picture p68: board 02-vco/electronics/ui-octave-switch/vco-ui.kicad_pcb from above]

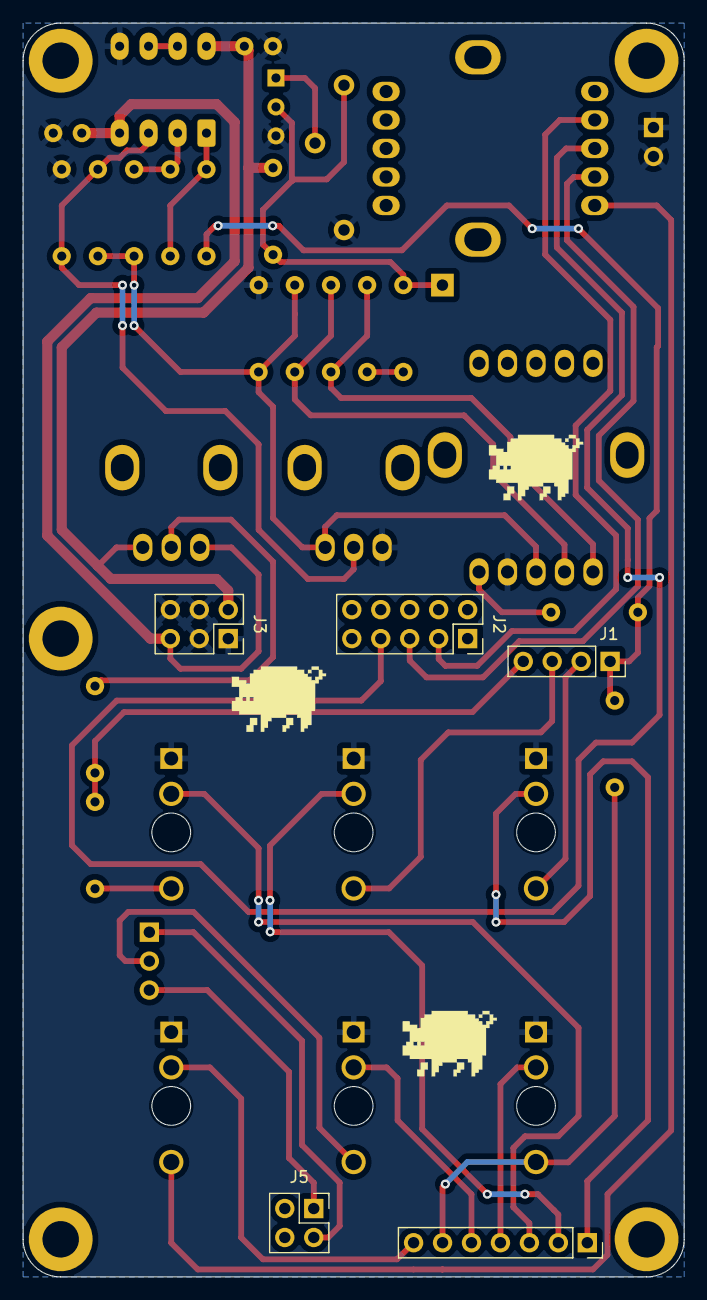
[picture p69: board 02-vco/electronics/ui-octave-switch/vco-ui.kicad_pcb from below]

Board: 2 copper layers, 58.0 x 110.0 mm, 43 parts (5 on the bottom side), 34 nets.
